agranlund/raven/hw/simm/programmer/README.md

# Raven ROM programmer

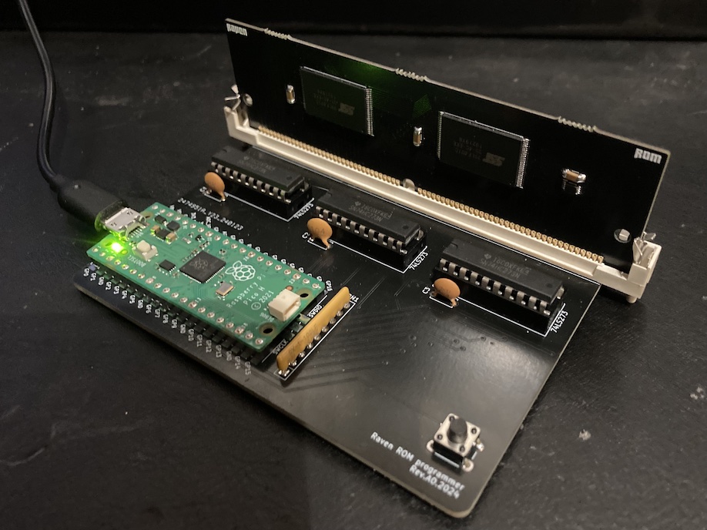
[picture p5: hw/simm/programmer/images/programmer.jpg]


## BOM

| Manufacturer | Part number | Value | Count | Ref |
|---|---|---|---|---|
| Vishay | K104K10X7RF53H5 | 0.1u | 3 | C101, C102, C103 |
| Texas Instruments | SN74HC273N | 74HC273 | 3 | U101, U103, U104 |
| Bourns | 4609X-101-102LF | 8x1K | 1 | RN101 |
| Alps Alpine | SKHHARA010 | button | 1 | SW101 |
| TE Connectivity | 5822030-3 | simm | 1 | J101 |
| Raspberry Pi | SC0915 | Pi Pico | 1 | U102 |
