agranlund/raven/hw/simm/rom_PLCC/README.md

# ROM module, socketed PLCC revision A0

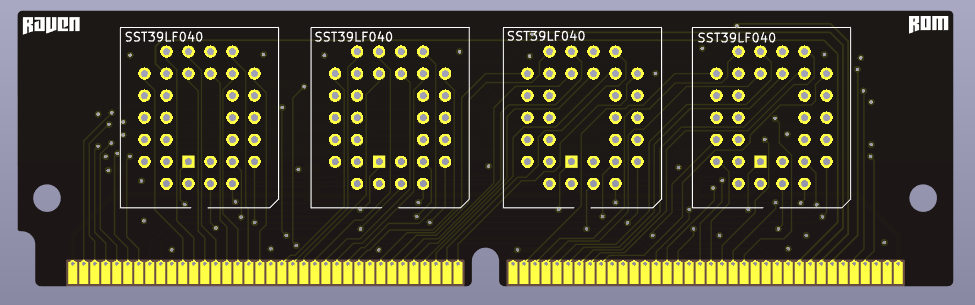
[picture p6: hw/simm/rom_PLCC/images/render.png]


Chip suggestions:
* SST39LF040-55 for 2MB
* SST39LF020-55 for 1MB

## BOM

| Manufacturer | Part number | Value | Count | Ref |
|---|---|---|---|---|
| Microchip | SST39LF040-55-4C-NHE-T | 4Mbit | 4 | U1, U2, U3, U4 |
| 3M | 8432-11B1-RK-TP | PLCC socket | 4 | U1, U2, U3, U4 |
| Kemet | C1206C104K5RACTU | 0.1u | 4 | C1, C2, C3, C4 |
