agranlund/raven/sw/dsp/asm56k/tools/readme.txt

Here are some DSP-Cross Development Utils - tested under 32bit and 64bit Linux

cldlod: 
  based upon original Motorola sources; 64bit fixed by me
  usage: cldlod cldfile [lodfile]

lod2p56:
  based upon the original Atari sources
  usage: lod2p56 lodfile [p56file]
