agranlund/raven/hw/raven/a1/upgrades/ideswap/README.md

# IDE Byteswap adapter

Converts an IDE interface between Intel and Motorola format (swaps high and low bytes)

Can be useful if you want Raven to have a legacy Atari (Motorola) IDE interface rather than the standard Intel interface it comes with.

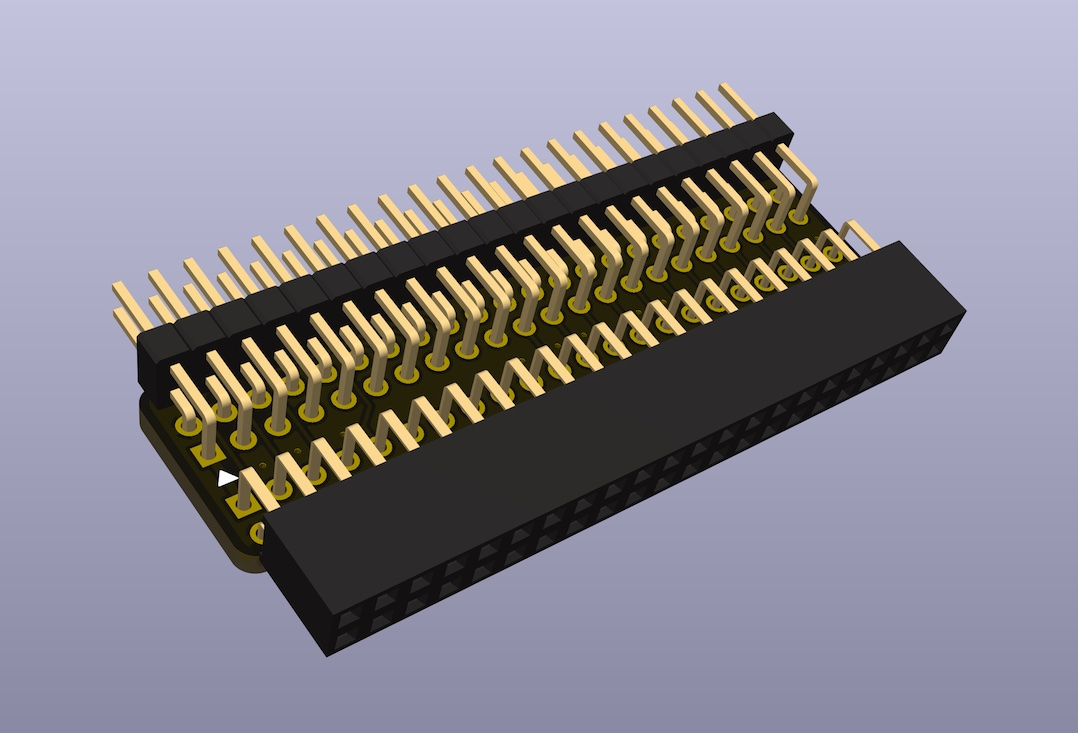
[picture p7: hw/raven/a1/upgrades/ideswap/ideswap.png]


## BOM

| Manufacturer  | Part number | Qty | Ref | Note |
|---|---|-----|---|---|
| Samtec | SQT-122-01-F-D-RA | 1 | J102 | Female right-angle |
| Amphenol | 58102-G61-22LF | 1 | J101 | Male right-angle |

(*) Molex 87833-4420 can be used if a shrouded male right-angle header is preferred.
