agranlund/raven/hw/raven/a1/upgrades/ckbd/README.md

# Eiffel upgrade module (rev.d) for Raven.A1

- Plugs into the Eiffel socket instead of the Eiffel PIC.
- Retains support for PS/2 mouse+keyboard, joystick and motherboard temperature sensor.
- Adds USB mouse and keyboard support on an internal USB header.
- Adds support for legacy Atari and Amiga mice (*)
- Adds support for reading CPU temperature (*)
- Adds support for software controlled shutdown (*)

### Firmware:
Binary, sourcecode, and programming instructions can be found here:
* [ckbd firmware](../../../../fw/ckbd/) 

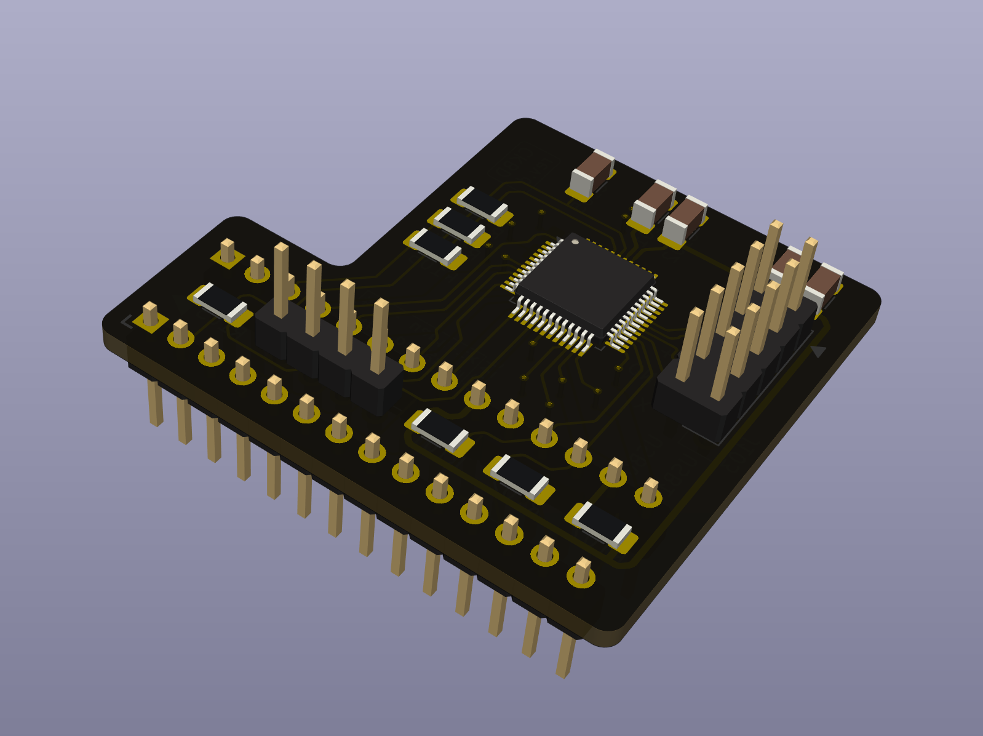
[picture p8: hw/raven/a1/upgrades/ckbd/ckbd.png]


(*) Features marked with an asterix requires soldering patch wires on the motherboard.
All solder points are available on through hole components and can be done on the underside of the motherboard.

#### Support for right mouse button on Legacy mice (not needed for USB or PS2)
- J606:A9  <-> J606:B6 (mouse right button - joystick1 fire button)
#### Support for CPU temperature readout
- U107:M15 <-> U107:M16 (CPU Therm1 - GND)
- U107:L15 <-> U301:26 (CPU Therm0 - Eiffel:Temp2)
#### Support for software controlled shutdown
- SW201:2 <-> U301:25 (PWR switch - Eiffel:PwrOff)

## BOM

| Manufacturer  | Part number | Value | Qty | Ref | Note |
|---|---|---|-----|---|---|
| WCH | CH559L | CH559L | 1 | U101 | |
| Yageo | RT1206FRE0710KL | 10K | 3 | R103,R105,R106 | |
| Yageo | RT1206FRE071KL | 1K | 4 | R101,R102,R104,R107 | |
| Kemet | C1206C105K4RACTU  | 1u | 2 | C103,C104 | |
| Kemet | C1206C104K5RACTU  | 0.1u | 2 | C102,C105 | |
| Kemet | C1206C334K5RACTU  | 0.33u | 1 | C101 | |
| ? | pinheader round | 1x14 | 2 | J101,J102 | (1)  |
| ? | pinheader square  | 2x5 | 1 | J103 | (2)  |
| ? | pinheader square  | 1x4 | 1 | J104 | (2)  |

(1) J101,J102 needs to be round machined pins that can fit in a dip socket.
40-pin breakaway strips can be found here:
https://www.exxosforum.co.uk/atari/store2/#0132

(2) J103,J104 are standard square pin headers which can be found anywhere.
40-pin breakaway strips can be found here:
https://www.exxosforum.co.uk/atari/store2/#0158

## Notes for previous rev.c boards:

The eiffel controlled fan does not work in the previous version of this board.

This can be fixed by soldering a ~1K resistor connecting pins FAN1 and +5V which are both found on the right row of the Eiffel connector.
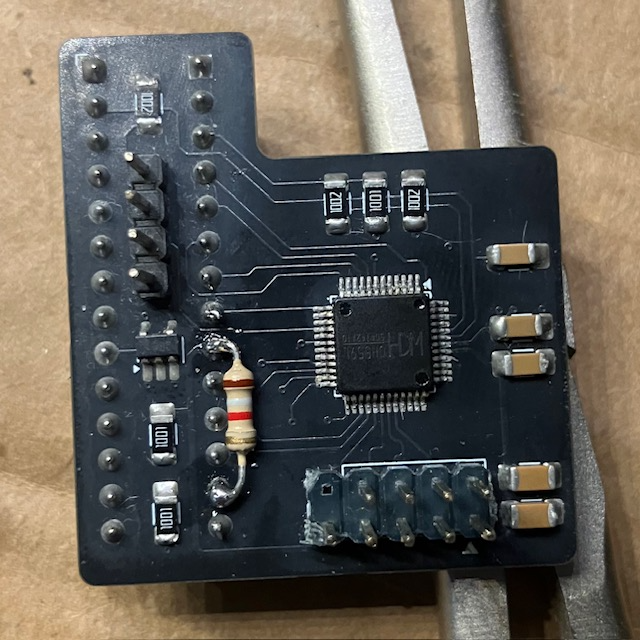
[picture p9: hw/raven/a1/upgrades/ckbd/ckbd_revc_fix.png]
