agranlund/raven/hw/isa/template_16bit/README.md

# Blank template
(untested)

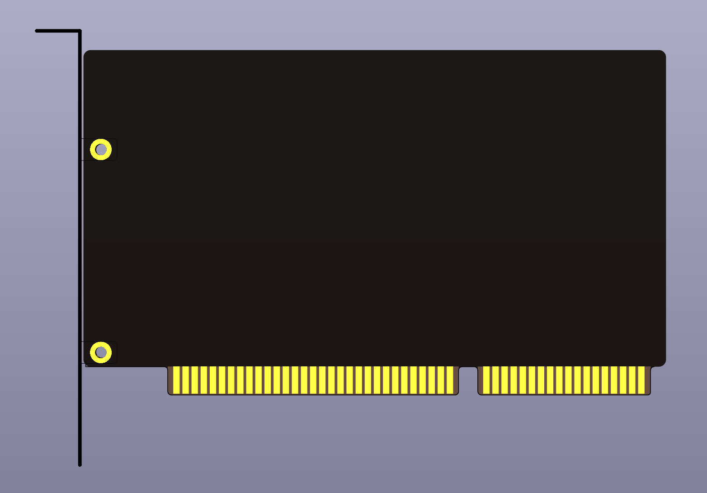
[picture p15: hw/isa/template_16bit/images/render.png]
