agranlund/raven/sw/tools/mon/readme.txt

Raven monitor shell

usage: mon <parameter>

Interact with Raven debug monitor from the TOS shell.
Same functionality as when pressing the NMI switch and doing so over a serial connection.
Parameters can be passed to execute a single command instead of interacting with the full shell.

This file is free software  you can redistribute it and/or modify
it under the terms of the GNU General Public License as published by
the Free Software Foundation  either version 2, or (at your option)
any later version.

This file is distributed in the hope that it will be useful,
but WITHOUT ANY WARRANTY  without even the implied warranty of
MERCHANTABILITY or FITNESS FOR A PARTICULAR PURPOSE.  See the
GNU General Public License for more details.

You should have received a copy of the GNU General Public License
along with this program  if not, write to the Free Software
Foundation, Inc., 675 Mass Ave, Cambridge, MA 02139, USA.
