agranlund/raven/hw/simm/ram_8M10/README.md

# RAM module: 8MB / 10ns

# !DO NOT USE! NOT YET SUPPORTED BY RAVEN FIRMWARE

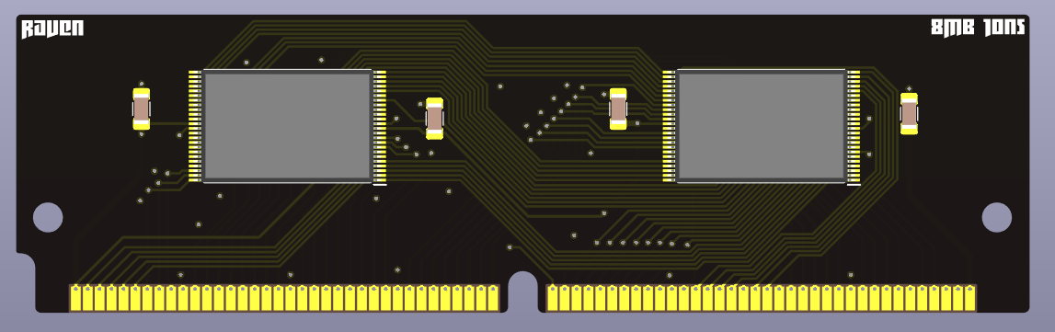
[picture p19: hw/simm/ram_8M10/images/render.png]


## BOM

| Manufacturer | Part number | Value | Count | Ref |
|---|---|---|---|---|
| ISSI | IS61WV204816BLL-10TLI | 16x2MBit | 2 | IC1, IC2 |
| Kemet | C1206C104K5RACTU | 0.1u | 4 | C1, C2, C3, C4 |
