agranlund/raven/hw/simm/breakout/README.md

# Debug module (untested)

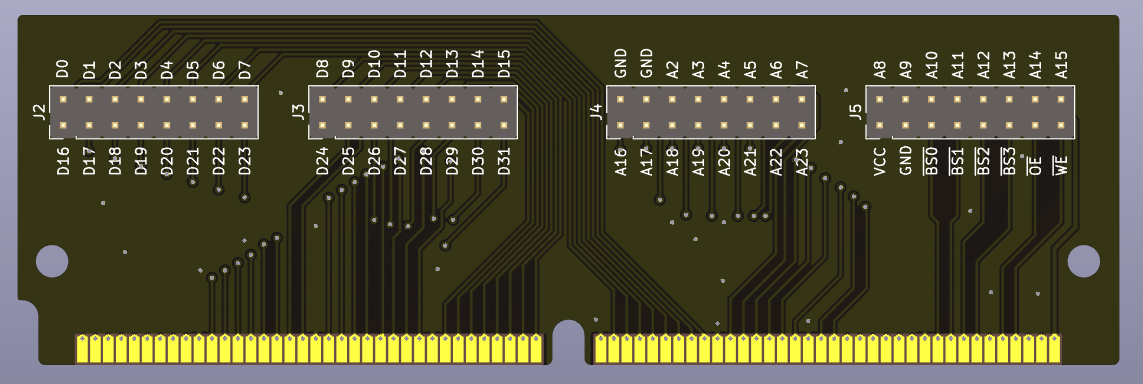
[picture p20: hw/simm/breakout/images/render.png]
