agranlund/raven/hw/simm/ram_16M55/README.md

# RAM module: 16MB / 55ns

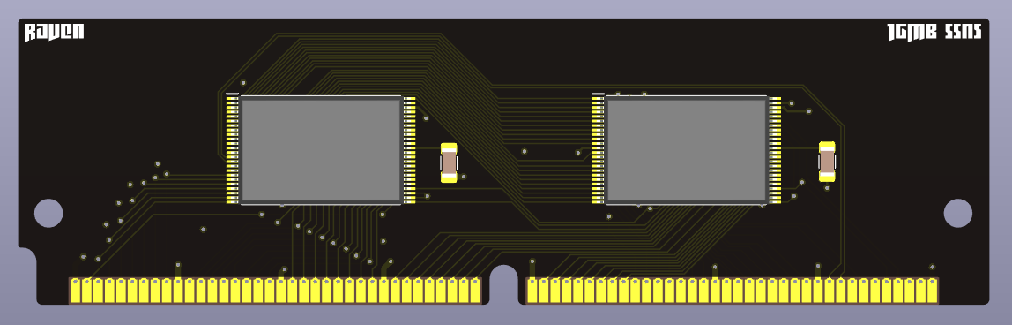
[picture p21: hw/simm/ram_16M55/images/render.png]


## BOM

| Manufacturer | Part number | Value | Count | Ref |
|---|---|---|---|---|
| Alliance Memory | AS6C6416-55TIN | 16x4MBit | 2 | IC1, IC2 |
| Kemet | C1206C104K5RACTU | 0.1u | 2 | C1, C2 |
