agranlund/raven/doc/img/board.gif

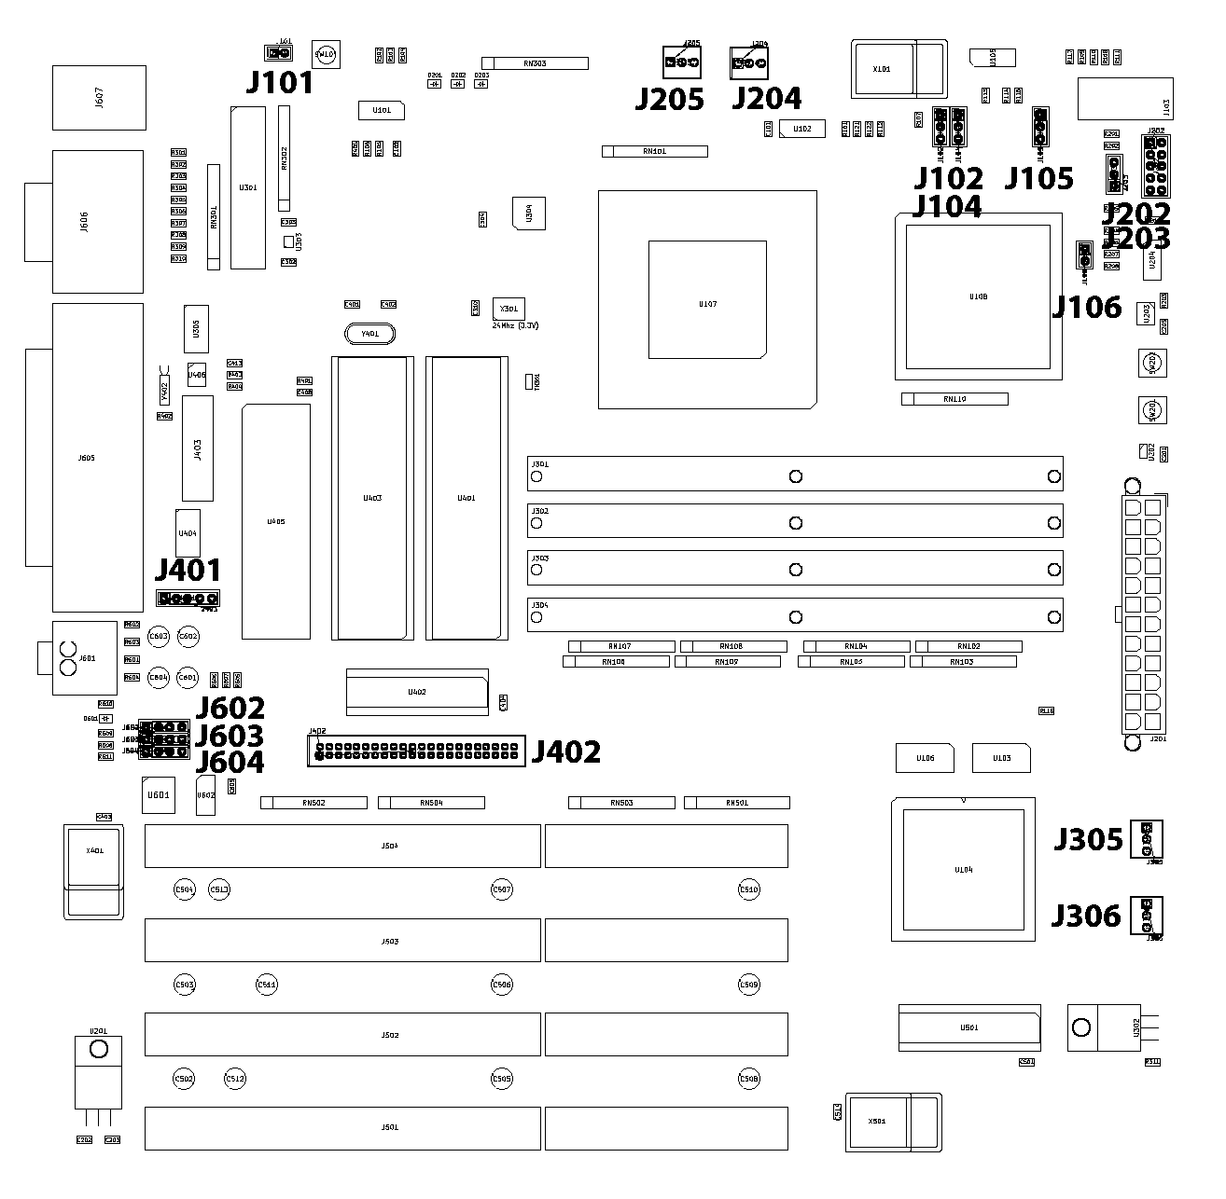
doc/img/board.gif
