agranlund/raven/doc/img/com.gif

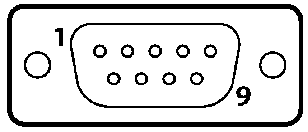
doc/img/com.gif
