agranlund/raven/doc/img/ide.gif

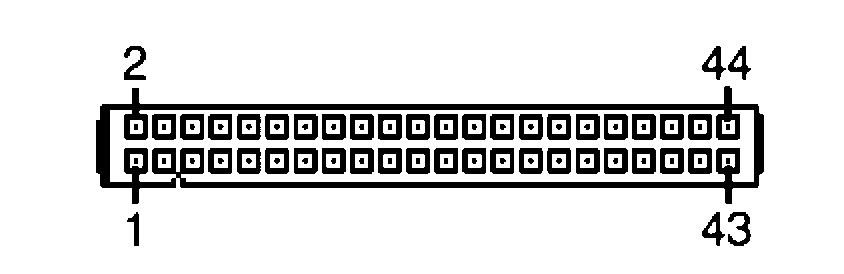
doc/img/ide.gif
