agranlund/raven/doc/img/ps2.gif

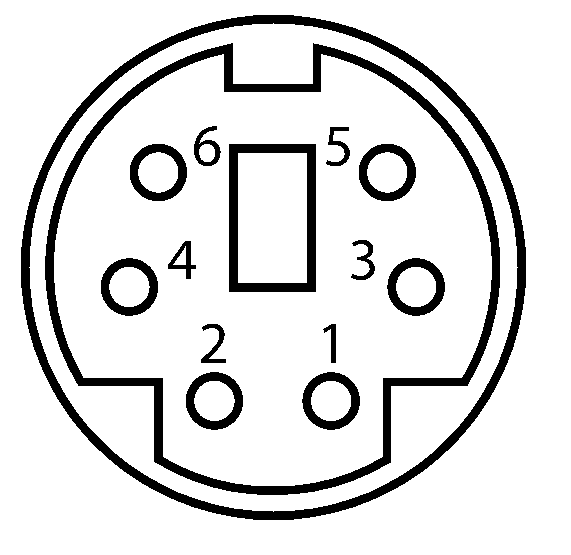
doc/img/ps2.gif
