agranlund/raven/doc/img/simm.gif

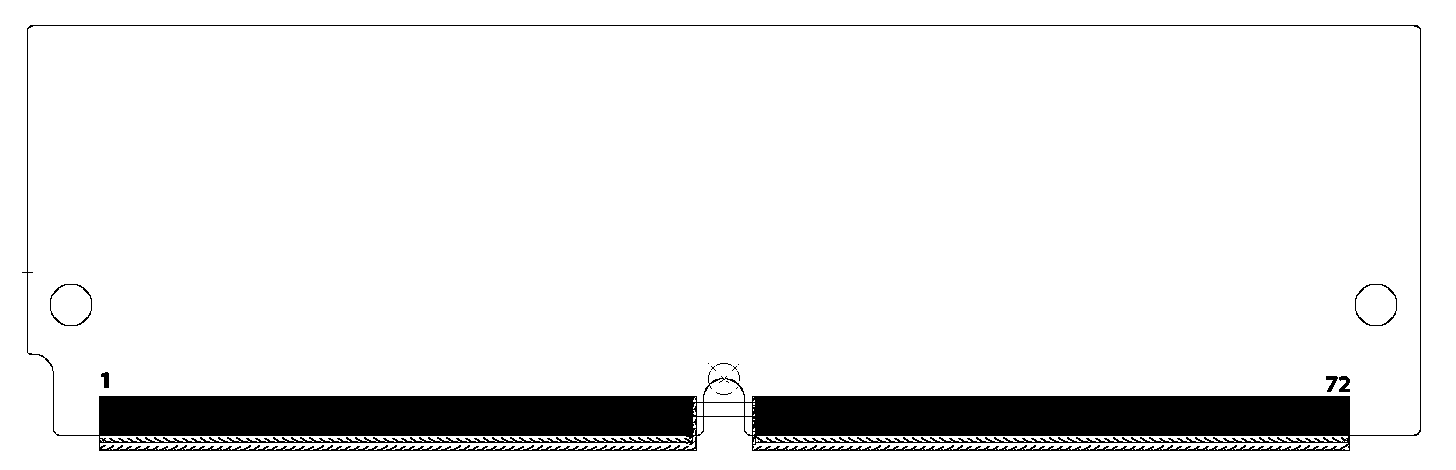
doc/img/simm.gif
