agranlund/raven/hw/raven/a0/images/raven_a0.jpg

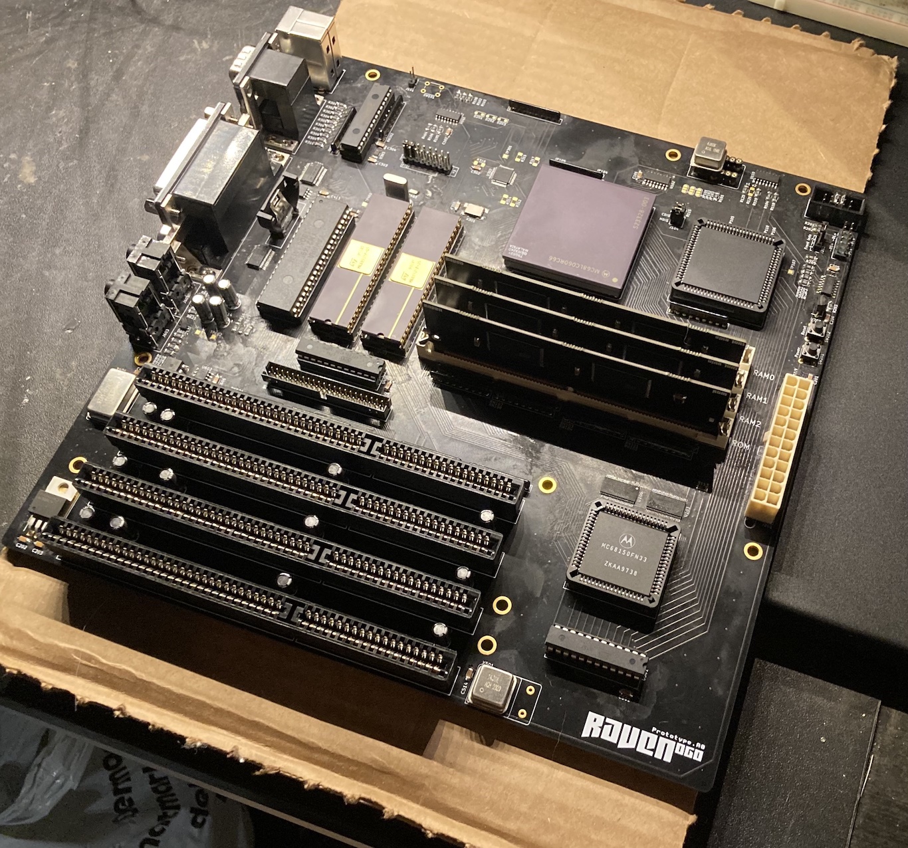
hw/raven/a0/images/raven_a0.jpg
