agranlund/raven/hw/raven/a0/images/raven_a0_cased1.jpg

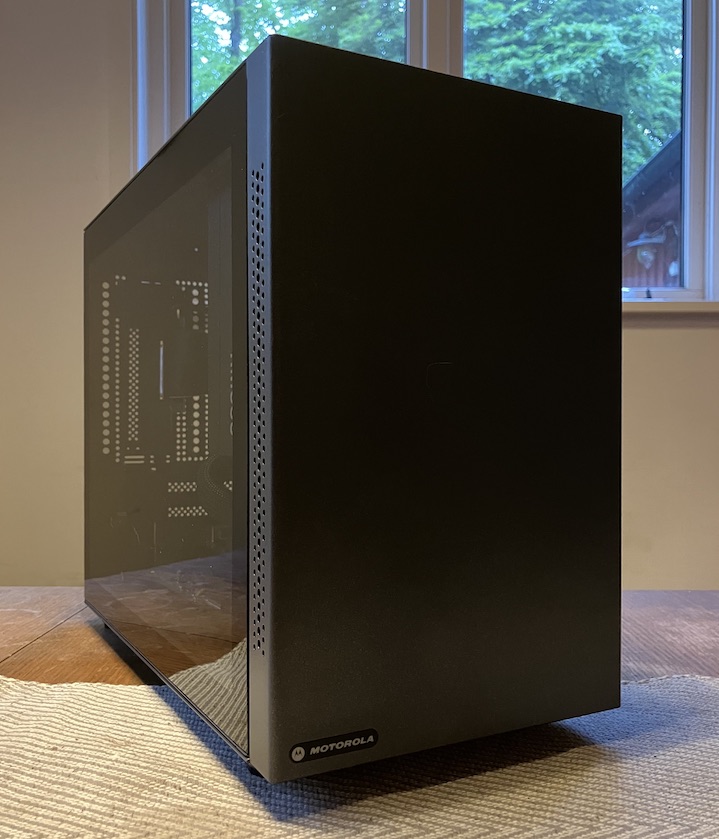
hw/raven/a0/images/raven_a0_cased1.jpg
