agranlund/raven/hw/simm/template/images/render.png

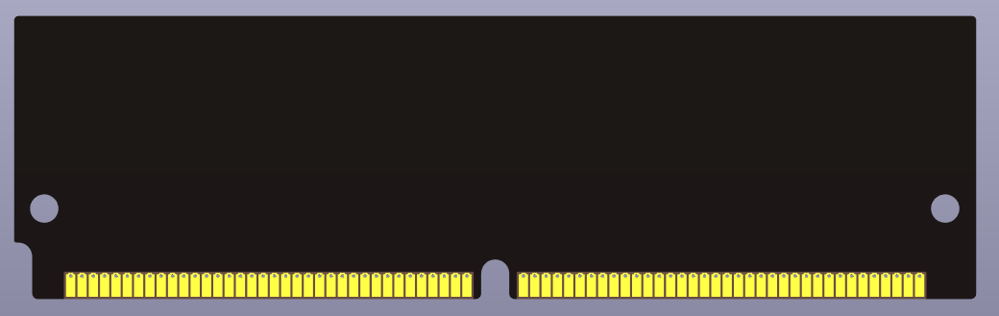
hw/simm/template/images/render.png
