agranlund/raven/sw/isa/drivers/picogus/hw-common/parts/USB-microB_U254-051T-4BH83-F1S.step

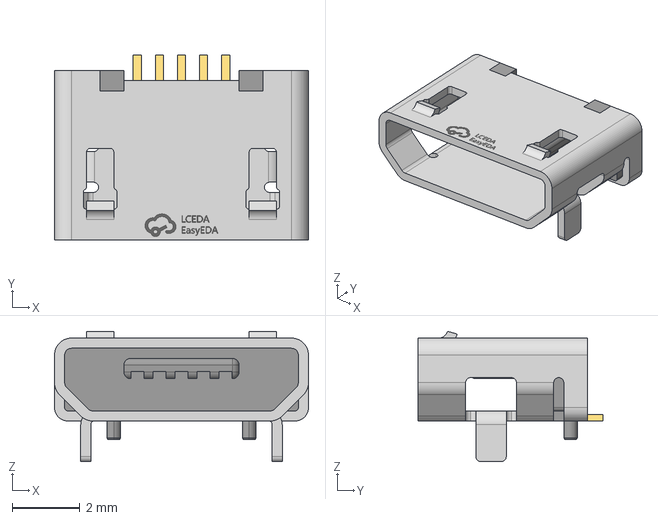
[picture p57: CAD file, 2024-07-06]
sw/isa/drivers/picogus/hw-common/parts/USB-microB_U254-051T-4BH83-F1S.step
7.50 x 5.45 x 3.85 mm
