agranlund/raven/sw/isa/drivers/picogus/isa-hand386 adapter/parts/RK10J12R0A0B.stp

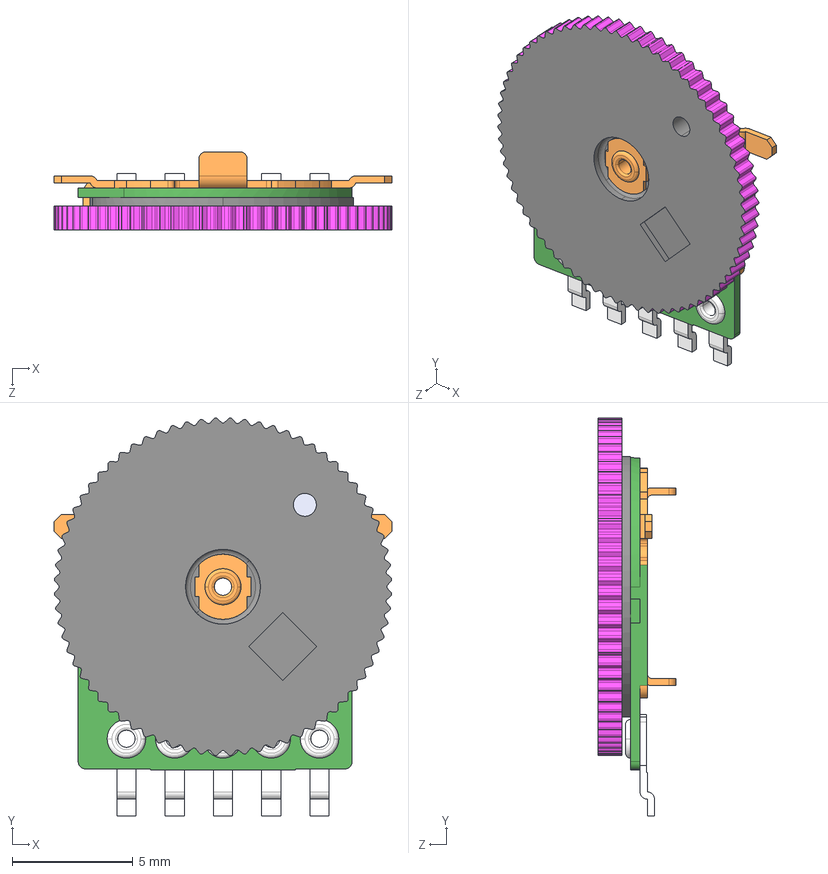
[picture p58: CAD file, 2024-07-06]
sw/isa/drivers/picogus/isa-hand386 adapter/parts/RK10J12R0A0B.stp
14.0 x 16.5 x 3.25 mm
