agranlund/raven/sw/isa/drivers/picogus/hw-common/parts/RK10J12R0A0B.step

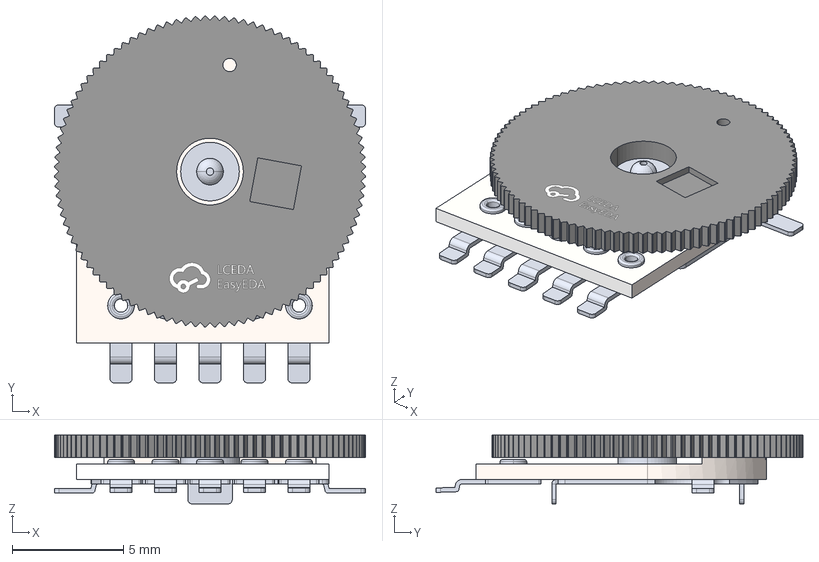
[picture p59: CAD file, 2024-07-06]
sw/isa/drivers/picogus/hw-common/parts/RK10J12R0A0B.step
14.0 x 16.5 x 3.10 mm
