agranlund/raven/sw/isa/drivers/picogus/hw-common/parts/keystone-9202-maxconnector.step

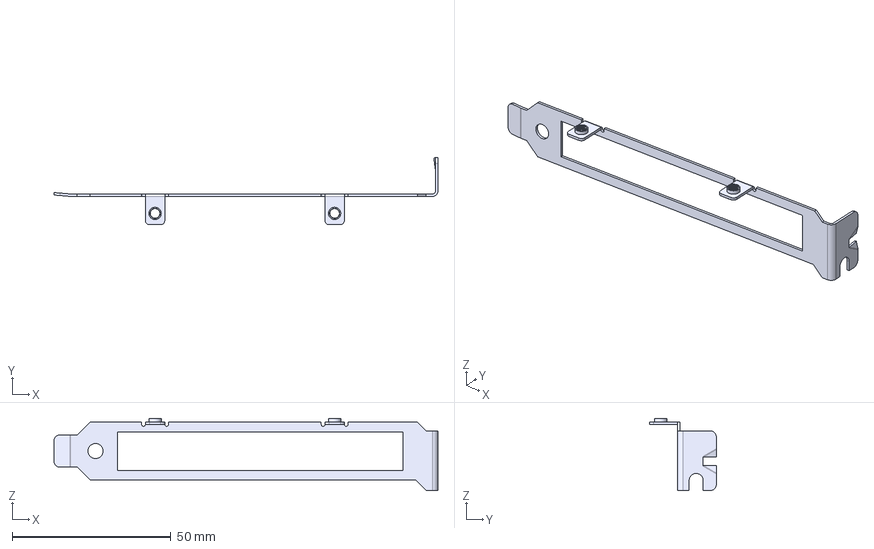
[picture p60: CAD file, 2024-07-06]
sw/isa/drivers/picogus/hw-common/parts/keystone-9202-maxconnector.step
120.9 x 21.2 x 22.7 mm
