agranlund/raven/sw/isa/drivers/picogus/hw-common/parts/PJ-210B.step

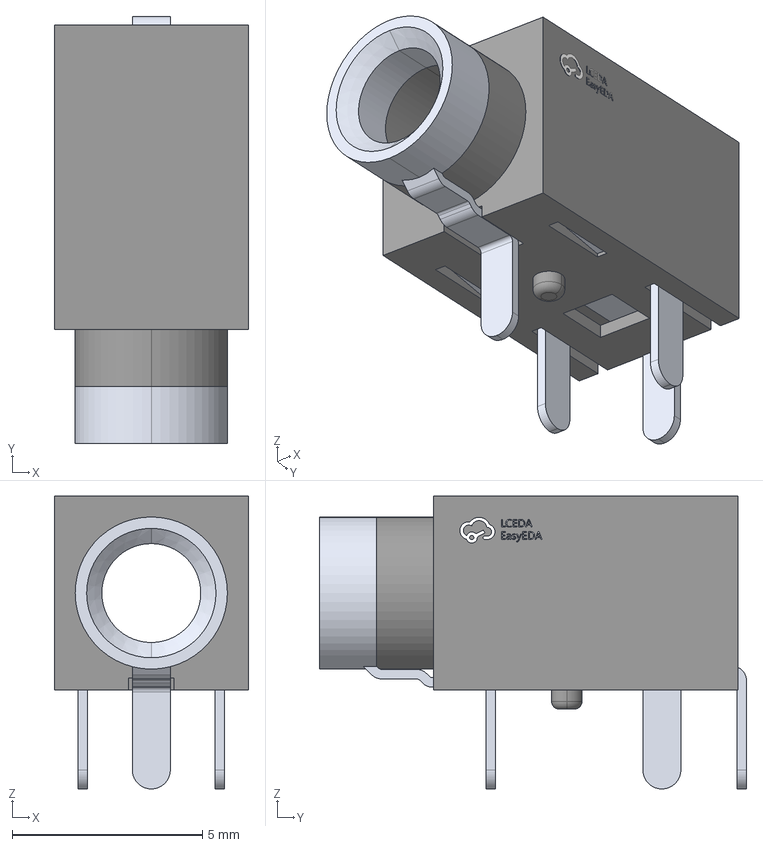
[picture p61: CAD file, 2024-07-06]
sw/isa/drivers/picogus/hw-common/parts/PJ-210B.step
5.11 x 11.2 x 7.70 mm
