agranlund/raven/sw/isa/drivers/picogus/hw-common/parts/TL3305BFxxxxG.stp

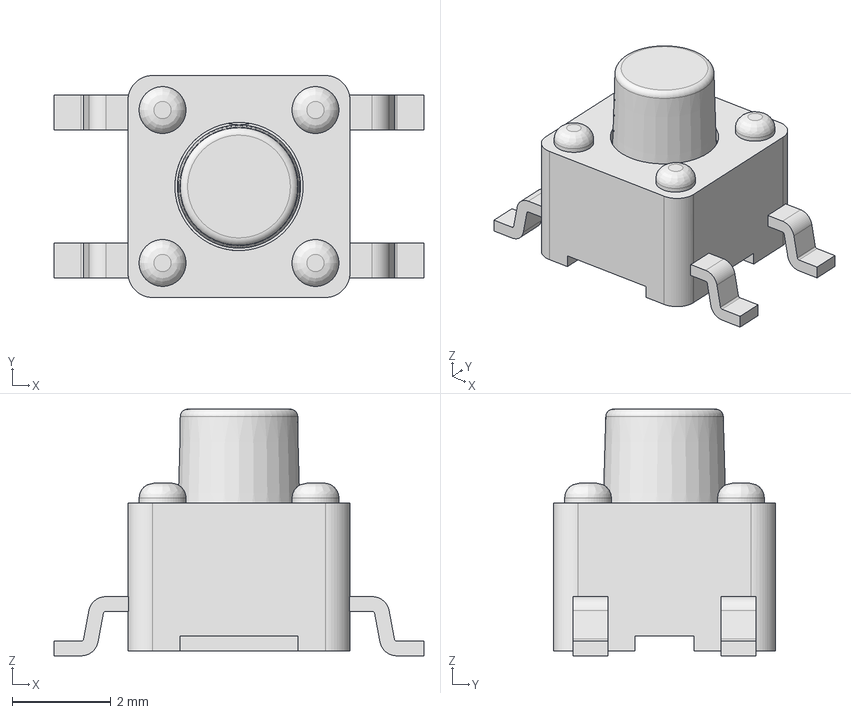
[picture p62: CAD file, 2024-07-06]
sw/isa/drivers/picogus/hw-common/parts/TL3305BFxxxxG.stp
7.50 x 4.50 x 5.00 mm
