agranlund/raven/sw/isa/drivers/picogus/hw-common/parts/CUI_DEVICES_SJ1-3533NG.step

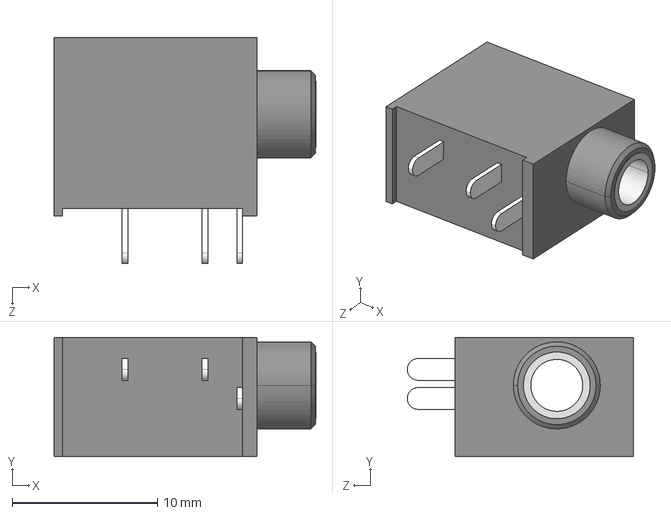
[picture p63: CAD file, 2024-07-06]
sw/isa/drivers/picogus/hw-common/parts/CUI_DEVICES_SJ1-3533NG.step
18.1 x 8.20 x 15.6 mm
