agranlund/raven/sw/isa/drivers/picogus/hw-common/parts/USB-A_902-131A1011D10100.step

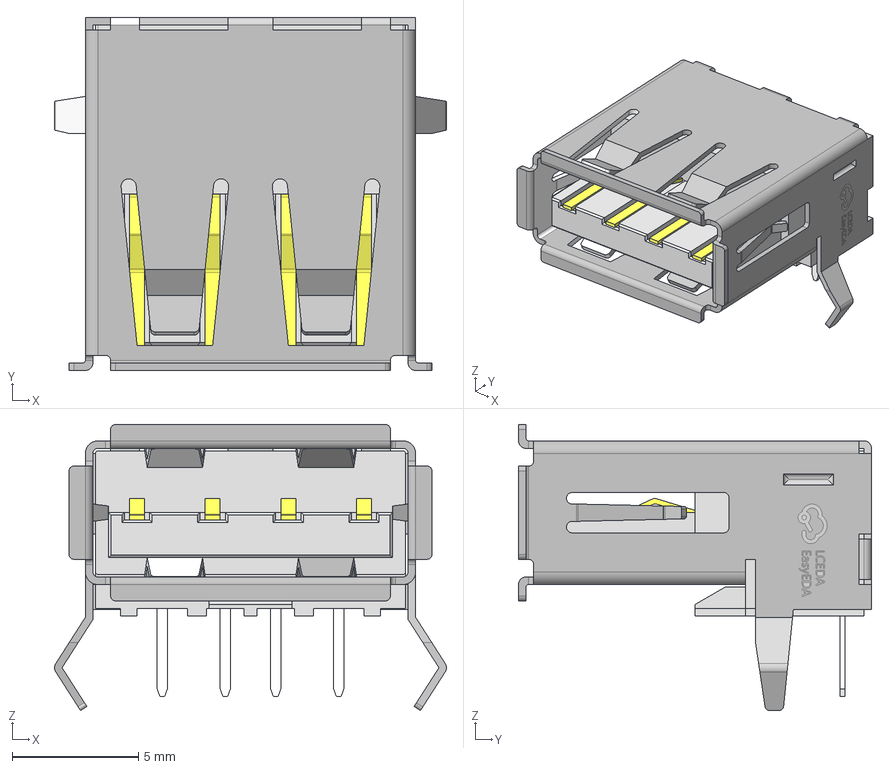
[picture p64: CAD file, 2024-07-06]
sw/isa/drivers/picogus/hw-common/parts/USB-A_902-131A1011D10100.step
15.5 x 14.0 x 11.3 mm
