agranlund/raven/sw/rvnova/test/scroll.bmp

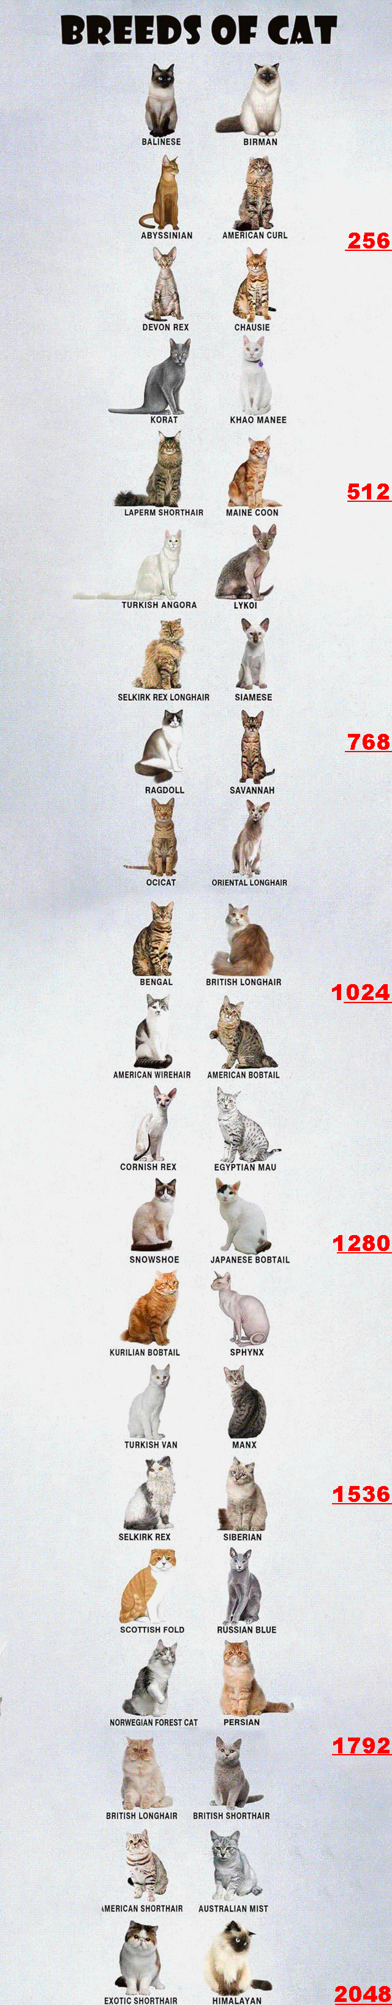
sw/rvnova/test/scroll.bmp
