agranlund/raven/hw/simm/breakout/simm72_breakout.kicad_pcb

## KiCad design hw/simm/breakout/simm72_breakout.kicad_pcb (2024-06-06)

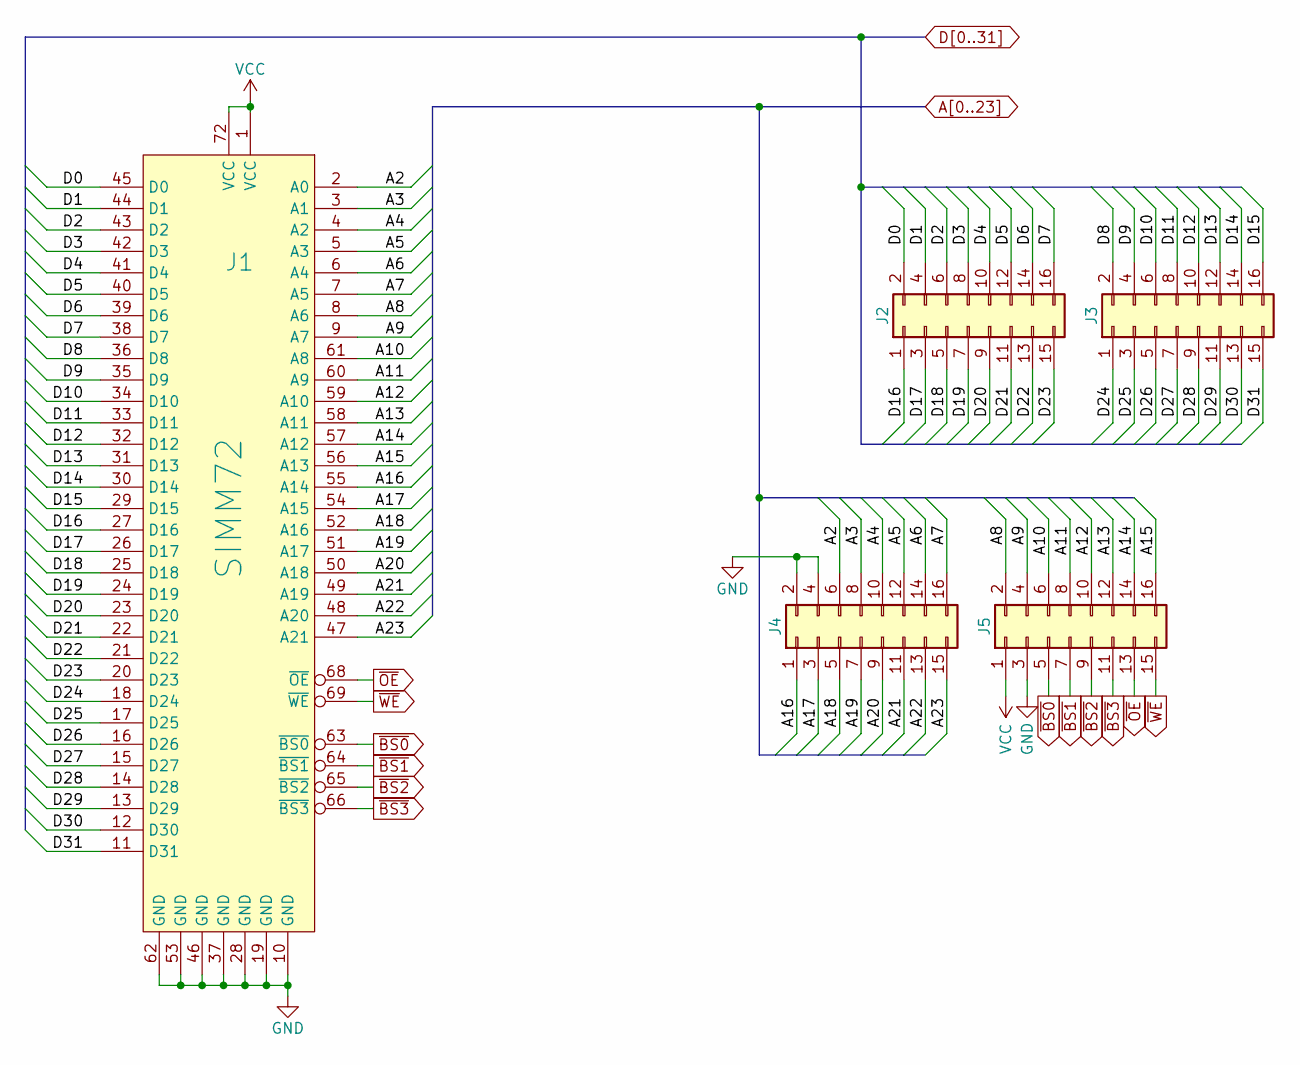
[picture p116: schematic simm72_breakout.kicad_sch, Raven SIMM breakout]

Parts:
J1: SIMM72; SIMM72_edge
J2, J3, J4, J5: Conn_02x08_Row_Letter_Last; PinHeader_2x08_P2.54mm_Vertical

Connections:
A2: J1.2 (A0), J4.6
A3: J1.3 (A1), J4.8
A4: J1.4 (A2), J4.10
A5: J1.5 (A3), J4.12
A6: J1.6 (A4), J4.14
A7: J1.7 (A5), J4.16
A8: J1.8 (A6), J5.2
A9: J1.9 (A7), J5.4
A10: J1.61 (A8), J5.6
A11: J1.60 (A9), J5.8
A12: J1.59 (A10), J5.10
A13: J1.58 (A11), J5.12
A14: J1.57 (A12), J5.14
A15: J1.56 (A13), J5.16
A16: J1.55 (A14), J4.1
A17: J1.54 (A15), J4.3
A18: J1.52 (A16), J4.5
A19: J1.51 (A17), J4.7
A20: J1.50 (A18), J4.9
A21: J1.49 (A19), J4.11
A22: J1.48 (A20), J4.13
A23: J1.47 (A21), J4.15
D0: J1.45 (D0), J2.2
D1: J1.44 (D1), J2.4
D2: J1.43 (D2), J2.6
D3: J1.42 (D3), J2.8
D4: J1.41 (D4), J2.10
D5: J1.40 (D5), J2.12
D6: J1.39 (D6), J2.14
D7: J1.38 (D7), J2.16
D8: J1.36 (D8), J3.2
D9: J1.35 (D9), J3.4
D10: J1.34 (D10), J3.6
D11: J1.33 (D11), J3.8
D12: J1.32 (D12), J3.10
D13: J1.31 (D13), J3.12
D14: J1.30 (D14), J3.14
D15: J1.29 (D15), J3.16
D16: J1.27 (D16), J2.1
D17: J1.26 (D17), J2.3
D18: J1.25 (D18), J2.5
D19: J1.24 (D19), J2.7
D20: J1.23 (D20), J2.9
D21: J1.22 (D21), J2.11
D22: J1.21 (D22), J2.13
D23: J1.20 (D23), J2.15
D24: J1.18 (D24), J3.1
D25: J1.17 (D25), J3.3
D26: J1.16 (D26), J3.5
D27: J1.15 (D27), J3.7
D28: J1.14 (D28), J3.9
D29: J1.13 (D29), J3.11
D30: J1.12 (D30), J3.13
D31: J1.11 (D31), J3.15
GND: J1.10 (GND), J1.19 (GND), J1.28 (GND), J1.37 (GND), J1.46 (GND), J1.53 (GND), J1.62 (GND), J4.2, J4.4, J5.3
VCC: J1.1 (VCC), J1.72 (VCC), J5.1
~BS0: J1.63 (~BS0), J5.5
~BS1: J1.64 (~BS1), J5.7
~BS2: J1.65 (~BS2), J5.9
~BS3: J1.66 (~BS3), J5.11
~OE: J1.68 (~OE), J5.13
~WE: J1.69 (~WE), J5.15

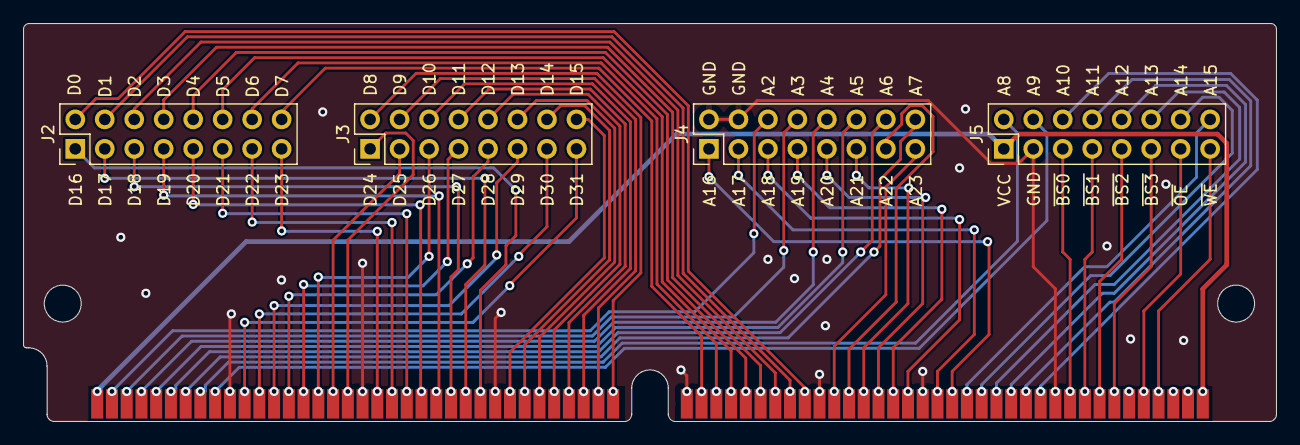
[picture p117: board simm72_breakout.kicad_pcb from above]

Board: 2 copper layers, 108.0 x 34.3 mm, 5 parts (0 on the bottom side), 62 nets.
