agranlund/raven/sw/purec/src/crosstos/abin/pc/INCLUDE/TOS.H

#define __TOS
typedef struct
{
        unsigned char maxlen;
        unsigned char actuallen;
        char    buffer[255];
} LINE;
typedef struct
{
    char            d_reserved[21];
    unsigned char   d_attrib;
    unsigned int    d_time;
    unsigned int    d_date;
    unsigned long   d_length;
    char            d_fname[14];
} DTA;
typedef struct
{
    unsigned long   b_free;
    unsigned long   b_total;
    unsigned long   b_secsiz;
    unsigned long   b_clsiz;
} DISKINFO;
typedef struct baspag
{
        void    *p_lowtpa;
        void    *p_hitpa;
        void    *p_tbase;
        long    p_tlen;
        void    *p_dbase;
        long    p_dlen;
        void    *p_bbase;
        long    p_blen;
        DTA     *p_dta;
        struct baspag *p_parent;
        long    p_resrvd0;
        char    *p_env;
        char    p_stdfh[6];
        char    p_resrvd1;
        char    p_curdrv;
        long    p_resrvd2[18];
        char    p_cmdlin[128];
} BASPAG;
typedef struct
{
        int     recsiz;
        int     clsiz;
        int     clsizb;
        int     rdlen;
        int     fsiz;
        int     fatrec;
        int     datrec;
        int     numcl;
        int     bflags;
} BPB;
typedef struct
{
        unsigned int  time;
        unsigned int  date;
} DOSTIME;
typedef struct
{
        void    *ibuf;
        int     ibufsiz;
        int     ibufhd;
        int     ibuftl;
        int     ibuflow;
        int     ibufhi;
} IOREC;
typedef struct
{
        void    (*kb_midivec)();
        void    (*kb_vkbderr)();
        void    (*kb_vmiderr)();
        void    (*kb_statvec)();
        void    (*kb_mousevec)();
        void    (*kb_clockvec)();
        void    (*kb_joyvec)();
        void    (*kb_midisys)();
        void    (*kb_kbdsys)();
} KBDVBASE;
typedef struct
{
        unsigned char   length;
        char            command_tail[128];
} COMMAND;
typedef struct
{
        char    topmode;
        char    buttons;
        char    x_scale;
        char    y_scale;
        int     x_max;
        int     y_max;
        int     x_start;
        int     y_start;
} MOUSE;
typedef struct
{
        void    *pb_scrptr;
        int     pb_offset;
        int     pb_width;
        int     pb_height;
        int     pb_left;
        int     pb_right;
        int     pb_screz;
        int     pb_prrez;
        void    *pb_colptr;
        int     pb_prtype;
        int     pb_prport;
        void    *pb_mask;
} PBDEF;
typedef struct
{
        char *unshift;
        char *shift;
        char *capslock;
} KEYTAB;
typedef struct __md
{
        struct __md *m_link;
        void        *m_start;
        long        m_length;
        BASPAG      *m_own;
} MD;
typedef struct
{
        MD *mp_mfl;
        MD *mp_mal;
        MD *mp_rover;
} MPB;
typedef struct
{
        int   (*Bconstat) ();
        long  (*Bconin) ();
        int   (*Bcostat) ();
        void  (*Bconout) ();
        long  (*Rsconf) ();
        IOREC *iorec;
} MAPTAB;
typedef struct
{
        MAPTAB *maptab;
        int    maptabsize;
} BCONMAP;
typedef struct _syshdr
{
    unsigned       os_entry;
    unsigned       os_version;
    void           *os_start;
    struct _syshdr *os_base;
    void           *os_membot;
    void           *os_rsv1;
    long           *os_magic;
    long           os_gendat;
    int            os_palmode;
    int            os_gendatg;
    void           *_root;
    long           *kbshift;
    BASPAG         **_run;
    void           *p_rsv2;
} SYSHDR;
#define FA_READONLY     0x01
#define FA_HIDDEN       0x02
#define FA_SYSTEM       0x04
#define FA_VOLUME       0x08
#define FA_SUBDIR       0x10
#define FA_ARCHIVE      0x20
#define FO_READ         0
#define FO_WRITE        1
#define FO_RW           2
extern BASPAG *_BasPag;
extern long _PgmSize;
long    gemdos( void, ... );
long    bios( void, ... );
long    xbios( void, ... );
void    Pterm0( void );
long    Cconin( void );
void    Cconout( int c );
int     Cauxin( void );
void    Cauxout( int c );
int     Cprnout( int c );
long    Crawio( int w );
long    Crawcin( void );
long    Cnecin( void );
int     Cconws( const char *buf );
void    Cconrs( LINE *buf );
int     Cconis( void );
long    Dsetdrv( int drv );
int     Cconos( void );
int     Cprnos( void );
int     Cauxis( void );
int     Cauxos( void );
int     Dgetdrv( void );
void    Fsetdta( DTA *buf );
long    Super( void *stack );
unsigned int  Tgetdate( void );
unsigned int Tsetdate( unsigned int date );
unsigned int  Tgettime( void );
unsigned int  Tsettime( unsigned int time );
DTA     *Fgetdta( void );
int     Sversion( void );
void    Ptermres( long keepcnt, int retcode );
int     Dfree( DISKINFO *buf, int driveno );
int     Dcreate( const char *path );
int     Ddelete( const char *path );
int     Dsetpath( const char *path );
long    Fcreate( const char *filename, int attr );
long    Fopen( const char *filename, int mode );
int     Fclose( int handle );
long    Fread( int handle, long count, void *buf );
long    Fwrite( int handle, long count, void *buf );
int     Fdelete( const char *filename );
long    Fseek( long offset, int handle, int seekmode );
int     Fattrib( const char *filename, int wflag, int attrib );
long    Fdup( int handle );
long    Fforce( int stch, int nonstdh );
int     Dgetpath( char *path, int driveno );
void    *Malloc( long number );
int     Mfree( void *block );
int     Mshrink( int zero, void *block, long newsiz );
long    Pexec( int mode, char *ptr1, void *ptr2, void *ptr3 );
void    Pterm( int retcode );
int     Fsfirst( const char *filename, int attr );
int     Fsnext( void );
int     Frename( int zero, const char *oldname, const char *newname );
int     Fdatime( DOSTIME *timeptr, int handle, int wflag );
void    *Mxalloc( long number, int mode );
long    Maddalt( void *start, long size );
long    Flock( int handle, int mode, long start, long length );
void    Getmpb( MPB *ptr );
int     Bconstat( int dev );
long    Bconin( int dev );
void    Bconout( int dev, int c );
long    Rwabs( int rwflag, void *buf, int cnt, int recnr, int dev );
void    (*Setexc( int number, void (*exchdlr)() )) ();
long    Tickcal( void );
BPB     *Getbpb( int dev );
long    Bcostat( int dev );
long    Mediach( int dev );
long    Drvmap( void );
long    Kbshift( int mode );
void    Initmouse( int type, MOUSE *par, void (*mousevec)() );
void    *Ssbrk( int count );
void    *Physbase( void );
void    *Logbase( void );
int     Getrez( void );
void    Setscreen( void *laddr, void *paddr, int rez );
void    Setpalette( void *pallptr );
int     Setcolor( int colornum, int color );
int     Floprd( void *buf, void *filler, int devno, int sectno,
               int trackno, int sideno, int count );
int     Flopwr( void *buf, void *filler, int devno, int sectno,
               int trackno, int sideno, int count );
int     Flopfmt( void *buf, void *filler, int devno, int spt, int trackno,
                int sideno, int interlv, long magic, int virgin );
void    Midiws( int cnt, void *ptr );
void    Mfpint( int erno, void (*vector)() );
IOREC   *Iorec( int dev );
long    Rsconf( int baud, int ctr, int ucr, int rsr, int tsr, int scr );
KEYTAB  *Keytbl( void *unshift, void *shift, void *capslock );
long    Random( void );
void    Protobt( void *buf, long serialno, int disktype, int execflag );
int     Flopver( void *buf, void *filler, int devno, int sectno,
                int trackno, int sideno, int count );
void    Scrdmp( void );
int     Cursconf( int func, int rate );
void    Settime( unsigned long time );
unsigned long  Gettime( void );
void    Bioskeys( void );
void    Ikbdws( int count, void *ptr );
void    Jdisint( int number );
void    Jenabint( int number );
char    Giaccess( char data, int regno );
void    Offgibit( int bitno );
void    Ongibit( int bitno );
void    Xbtimer( int timer, int control, int data, void (*vector)() );
void    *Dosound( void *buf );
int     Setprt( int config );
KBDVBASE *Kbdvbase( void );
int     Kbrate( int initial, int repeat );
void    Prtblk( PBDEF *par );
void    Vsync( void );
long    Supexec( long (*func)() );
void    Puntaes( void );
int     Floprate( int devno, int newrate );
int     Blitmode( int mode );
int     DMAread( long sector, int count, void *buffer, int devno );
int     DMAwrite( long sector, int count, void *buffer, int devno );
int     NVMaccess( int opcode, int start, int count, void *buffer );
long    Bconmap( int devno );
int     Esetshift( int shftMode );
int     Egetshift( void );
int     EsetBank( int bankNum );
int     EsetColor( int colorNum, int color );
void    EsetPalette( int colorNum, int count, int *palettePtr );
void    EgetPalette( int colorNum, int count, int *palettePtr );
int     EsetGray( int swtch );
int     EsetSmear( int swtch );
#define NSIG       31
#define SIGNULL     0
#define SIGHUP      1
#define SIGINT      2
#define SIGQUIT     3
#define SIGILL      4
#define SIGTRAP     5
#define SIGABRT     6
#define SIGPRIV     7
#define SIGFPE      8
#define SIGKILL     9
#define SIGBUS     10
#define SIGSEGV    11
#define SIGSYS     12
#define SIGPIPE    13
#define SIGALRM    14
#define SIGTERM    15
#define SIGURG     16
#define SIGSTOP    17
#define SIGTSTP    18
#define SIGCONT    19
#define SIGCHLD    20
#define SIGTTIN    21
#define SIGTTOU    22
#define SIGIO      23
#define SIGXCPU    24
#define SIGXFSZ    25
#define SIGVTALRM  26
#define SIGPROF    27
#define SIGWINCH   28
#define SIGUSR1    29
#define SIGUSR2    30
#define SIG_DFL    0
#define SIG_IGN    1
#define S_IFMT  0170000
#define S_IFCHR 0020000
#define S_IFDIR 0040000
#define S_IFREG 0100000
#define S_IFIFO 0120000
#define S_IMEM  0140000
#define S_IFLNK 0160000
#define S_ISUID 04000
#define S_ISGID 02000
#define S_ISVTX 01000
#define S_IRUSR         0400
#define S_IWUSR         0200
#define S_IXUSR         0100
#define S_IRGRP         0040
#define S_IWGRP         0020
#define S_IXGRP         0010
#define S_IROTH         0004
#define S_IWOTH         0002
#define S_IXOTH         0001
#define DEFAULT_DIRMODE (0777)
#define DEFAULT_MODE    (0666)
typedef struct
{
        long     msg1;
        long     msg2;
        int      pid;
} MSG;
typedef struct
{
        unsigned int   mode;
        long           index;
        unsigned int   dev;
        unsigned int   reserved1;
        unsigned int   nlink;
        unsigned int   uid;
        unsigned int   gid;
        long           size;
        long           blksize;
        long           nblocks;
        int            mtime;
        int            mdate;
        int            atime;
        int            adate;
        int            ctime;
        int            cdate;
        int            attr;
        int            reserved2;
        long           reserved3[2];
} XATTR;
#define SA_NOCLDSTOP    1
typedef struct
{
        void    (*sa_handler)( long sig );
        long    sa_mask;
        int     sa_flags;
} SIGACTION;
int     Syield( void );
int     Fpipe( int *usrh );
int     Fcntl( int f, long arg, int cmd );
long    Finstat( int f );
long    Foutstat( int f );
long    Fgetchar( int f, int mode );
long    Fputchar( int f, long c, int mode );
long    Pwait( void );
int     Pnice( int delta );
int     Pgetpid( void );
int     Pgetppid( void );
int     Pgetpgrp( void );
int     Psetpgrp( int pid, int newgrp );
int     Pgetuid( void );
int     Psetuid( int id );
int     Pkill( int pid, int sig );
void    *Psignal( int sig, void *handler );
int     Pvfork( void );
int     Pgetgid( void );
int     Psetgid( int id );
long    Psigblock( long mask );
long    Psigsetmask( long mask );
long    Pusrval( long arg );
int     Pdomain( int newdom );
void    Psigreturn( void );
int     Pfork( void );
long    Pwait3( int flag, long *rusage );
int     Fselect( unsigned int timeout, long *rfds, long *wfds, long *xfds );
void    Prusage( long *r );
long    Psetlimit( int lim, long value );
long    Talarm( long secs );
void    Pause( void );
long    Sysconf( int n );
long    Psigpending( void );
long    Dpathconf( char *name, int n );
long    Pmsg( int mode, long mbox, MSG *msg );
long    Fmidipipe( int pid, int in, int out );
int     Prenice( int pid, int delta );
long    Dopendir( char *name, int flag );
long    Dreaddir( int buflen, long dir, char *buf );
long    Drewinddir( long dir );
long    Dclosedir( long dir );
long    Fxattr( int flag, char *name, XATTR *buf );
long    Flink( char *oldname, char *newname );
long    Fsymlink( char *oldname, char *newname );
long    Freadlink( int size, char *buf, char *name );
long    Dcntl( int cmd, char *name, long arg );
long    Fchown( char *name, int uid, int gid );
long    Fchmod( char *name, int mode );
long    Pumask( unsigned int mode );
long    Psemaphore( int mode, long id, long timeout );
long    Dlock( int mode, int drive );
void    Psigpause( unsigned long mask );
long    Psigaction( int sig, SIGACTION *act, SIGACTION *oact );
int     Pgeteuid( void );
int     Pgetegid( void );
#define VERTFLAG          0x0100
#define STMODES           0x0080
#define OVERSCAN          0x0040
#define PAL               0x0020
#define VGA               0x0010
#define TV                0x0000
#define COL80             0x08
#define COL40             0x00
#define BPS16             4
#define BPS8              3
#define BPS4              2
#define BPS2              1
#define BPS1              0
#define NUMCOLS           7
long    locksnd( void );
long    unlocksnd( void );
long    soundcmd( int mode, int data );
long    setbuffer( int reg, void *begaddr, void *endaddr );
long    setsndmode( int mode );
long    settracks( int playtracks, int rectracks );
long    setmontracks( int montrack );
long    setinterrupt( int src_inter, int cause );
long    buffoper( int mode );
long    dsptristate( int dspxmit, int dsprec );
long    gpio( int mode, int data );
long    devconnect( int src, int dst, int srcclk, int prescale,
                    int protocol );
long    sndstatus( int reset );
long    buffptr( long *ptr );
int     Dsp_LoadProg( char *file, int ability, char *buffer );
long    Dsp_LodToBinary( char *file, char *codeptr );
void    Dsp_DoBlock( char *data_in, long size_in, char *data_out,
                     long size_out );
void    Dsp_BlkHandShake( char *data_in, long size_in, char *data_out,
                          long size_out );
void    Dsp_BlkUnpacked( long *data_in, long size_in, long *data_out,
                         long size_out );
void    Dsp_InStream( char *data_in, long block_size, long num_blocks,
                      long *blocks_done );
void    Dsp_OutStream( char *data_out, long block_size, long num_blocks,
                       long *blocks_done );
void    Dsp_IOStream( char *data_in, char *data_out, long block_insize,
                      long block_outsize, long num_blocks,
                      long *blocks_done );
void    Dsp_RemoveInterrupts( int mask );
int     Dsp_GetWordSize( void );
int     Dsp_Lock( void );
void    Dsp_Unlock( void );
void    Dsp_Available( long *xavailable, long *yavailable );
int     Dsp_Reserve( long xreserve, long yreserve );
void    Dsp_ExecProg( char *codeptr, long codesize, int ability );
void    Dsp_ExecBoot( char *codeptr, long codesize, int ability );
void    Dsp_TriggerHC( int vector );
int     Dsp_RequestUniqueAbility( void );
int     Dsp_GetProgAbility( void );
void    Dsp_FlushSubroutines( void );
int     Dsp_LoadSubroutine( char *codeptr, long codesize, int ability );
int     Dsp_InqSubrAbility( int ability );
int     Dsp_RunSubroutine( int handle );
int     Dsp_Hf0( int flag );
int     Dsp_Hf1( int flag );
int     Dsp_Hf2( void );
int     Dsp_Hf3( void );
void    Dsp_BlkWords( void *data_in, long size_in, void *data_out,
                      long size_out );
void    Dsp_BlkBytes( void *data_in, long size_in, void *data_out,
                      long size_out );
char    Dsp_HStat( void );
void    Dsp_SetVectors( void (*receiver)( ), long (*transmitter)( ));
int     setmode( int modecode );
int     mon_type( void );
void    ext_sync( int flag );
