agranlund/raven/sw/rom/mon/hw/cpu.c

#include "hw/cpu.h"

#define VBR_PROXY_IN_ROM        1
#define PMMU_PAGESIZE           (4 * 1024UL)

extern NMIFunc_t   NMIFunc;
extern uint32_t    NMIBusy;

uint32_t*   vbrTable __attribute__((aligned(4)));
uint32_t*   mmuRootTable __attribute__((aligned(4)));
uint32_t*   mmuInvalidPtrTable __attribute__((aligned(4)));
uint32_t*   mmuInvalidPageTable __attribute__((aligned(4)));
uint32_t*   mmuInvalidPage __attribute__((aligned(4)));
uint32_t*   mmuInvalidPageDesc __attribute__((aligned(4)));


//-----------------------------------------------------------------------
// cpu
//-----------------------------------------------------------------------
void cpu_NullNMI(regs_t* r) {
}


bool cpu_Init()
{
    // set dummy nmi handler
    NMIFunc = cpu_NullNMI;
    NMIBusy = 0;

    uint32_t rev;
    cpu_Detect(&rev, 0);

    uint32_t pcr = 0;
    pcr |= (1 << 0);        // enable superscalar dispatch
    if ((rev == 1) || (rev == 5)) {
        pcr |= (1 << 5);    // disable store/load bypass (errata I14)
    }
    cpu_SetPCR(pcr);
    return true;
}


uint32_t cpu_Detect(uint32_t* revout, uint32_t* idout)
{
    uint32_t sku = CPU_UNKONWN;
    uint32_t rev = 1;

    uint32_t pcr = cpu_GetPCR();
    rev = (pcr >> 8) & 0xFF;
    if ((pcr & 0x000f0000) == 0)
        sku = CPU_68060;
    else if (rev == 4)
        sku = CPU_68LC060;
    else if (rev == 3)
        sku = CPU_68EC060;

    if (idout)
        *idout = pcr & 0xffffff00;

    if (revout)
        *revout = rev;

    return sku;
}


NMIFunc_t cpu_SetNMI(NMIFunc_t func)
{
    NMIFunc_t old = NMIFunc;
    NMIFunc = func;
    return old;
}


//-----------------------------------------------------------------------
// mmu
//-----------------------------------------------------------------------
uint32_t* mmu_Init(uint32_t unmapped_desc)
{
    mmuRootTable        = (uint32_t*) mem_LinearAlloc(128 * 4, 512);
    mmuInvalidPtrTable  = (uint32_t*) mem_LinearAlloc(128 * 4, 512);
    mmuInvalidPageTable = (uint32_t*) mem_LinearAlloc( 64 * 4, 256);
    mmuInvalidPageDesc  = (uint32_t*) mem_LinearAlloc(  1 * 4, 256);
    mmuInvalidPage      = (uint32_t*) mem_LinearAlloc(PMMU_PAGESIZE, PMMU_PAGESIZE);

    mmuInvalidPageDesc[0] = unmapped_desc ? unmapped_desc : (((uint32_t)mmuInvalidPage) | (PMMU_READWRITE | PMMU_CM_WRITETHROUGH));

    for (int i=0; i<PMMU_PAGESIZE/4; i++)
        mmuInvalidPage[i] = 0;

    for (int i=0; i<64; i++)
        mmuInvalidPageTable[i] = ((uint32_t)mmuInvalidPageDesc) | PMMU_INDIRECT;

    for (int i=0; i<128; i++)
        mmuInvalidPtrTable[i] = ((uint32_t)mmuInvalidPageTable) | PMMU_READWRITE;

    for (int i=0; i<128; i++)
        mmuRootTable[i] = ((uint32_t)mmuInvalidPtrTable) | PMMU_READWRITE;

    return mmuRootTable;
}


uint32_t* mmu_GetPageDescriptor(uint32_t log)
{
    const uint32_t ptrTableAddressMask = ~511UL;
    const uint32_t pageTableAddressMask = ~255UL;
    //const uint32_t pageAddressMask = ~(PMMU_PAGESIZE - 1);
    //uint32_t addr = log & ~(PMMU_PAGESIZE - 1);

    uint32_t rootIdx = (log >> 25) & 127;
    uint32_t ptrIdx  = (log >> 18) & 127;
    uint32_t pageIdx = (log >> 12) & 63;

    uint32_t* ptrTable = (uint32_t*) (mmuRootTable[rootIdx] & ptrTableAddressMask);
    if (ptrTable == mmuInvalidPtrTable) {
        ptrTable = (uint32_t*) mem_LinearAlloc(128 * 4, 512);
        for (int i=0; i<128; i++)
            ptrTable[i] = ((uint32_t)mmuInvalidPageTable) | PMMU_READWRITE;

        mmuRootTable[rootIdx] = ((uint32_t)ptrTable) | PMMU_READWRITE;
    }

    uint32_t* pageTable = (uint32_t*) (ptrTable[ptrIdx] & pageTableAddressMask);
    if (pageTable == mmuInvalidPageTable) {
        pageTable = (uint32_t*) mem_LinearAlloc(64 * 4, 256);
        for (int i=0; i<64; i++)
            pageTable[i] = ((uint32_t)mmuInvalidPageDesc) | PMMU_INDIRECT;
        ptrTable[ptrIdx] = ((uint32_t)pageTable) | PMMU_READWRITE;
    }

    return &pageTable[pageIdx];
}


void mmu_Map(uint32_t log, uint32_t phys, uint32_t size, uint32_t flags)
{
    const uint32_t pageAddressMask = ~(PMMU_PAGESIZE - 1);
    uint32_t end = (log + size + (PMMU_PAGESIZE - 1)) & pageAddressMask;
    uint32_t src = log & pageAddressMask;
    uint32_t dst = phys & pageAddressMask;

    while (src != end)
    {
        uint32_t* pageDescriptor = mmu_GetPageDescriptor(src);
        *pageDescriptor = flags | dst;
        src += PMMU_PAGESIZE;
        dst += PMMU_PAGESIZE;
    }
}


void mmu_Redirect(uint32_t logsrc, uint32_t logdst, uint32_t size)
{
    const uint32_t pageAddressMask = ~(PMMU_PAGESIZE - 1);
    uint32_t end = (logsrc + size + (PMMU_PAGESIZE - 1)) & pageAddressMask;
    uint32_t src = logsrc & pageAddressMask;
    uint32_t dst = logdst & pageAddressMask;

    while (src != end)
    {
        uint32_t* srcPageDescriptor = mmu_GetPageDescriptor(src);
        uint32_t* dstPageDescriptor = mmu_GetPageDescriptor(dst);
        *srcPageDescriptor = PMMU_INDIRECT | (uint32_t)dstPageDescriptor;
        src += PMMU_PAGESIZE;
        dst += PMMU_PAGESIZE;
    }
}

void mmu_Invalid(uint32_t log, uint32_t size)
{
    const uint32_t pageAddressMask = ~(PMMU_PAGESIZE - 1);
    uint32_t end = (log + size + (PMMU_PAGESIZE - 1)) & pageAddressMask;
    uint32_t src = log & pageAddressMask;

    while (src != end)
    {
        uint32_t* pageDescriptor = mmu_GetPageDescriptor(src);
        *pageDescriptor &= ~3UL;
        src += PMMU_PAGESIZE;
    }
}

// jmp ([0x08.w])  // 4ef0 01e1 0008
// jmp ([0x08.l])  // 4ef0 01f1 0000 0008

#if VBR_PROXY_IN_ROM
const uint16_t vbrProxy[] __attribute__((aligned(16))) = {
    0x4ef0, 0x01e1, 0x0000, 0x0000, 0x4ef0, 0x01e1, 0x0004, 0x0000, 0x4ef0, 0x01e1, 0x0008, 0x0000, 0x4ef0, 0x01e1, 0x000c, 0x0000,
    0x4ef0, 0x01e1, 0x0010, 0x0000, 0x4ef0, 0x01e1, 0x0014, 0x0000, 0x4ef0, 0x01e1, 0x0018, 0x0000, 0x4ef0, 0x01e1, 0x001c, 0x0000,
    0x4ef0, 0x01e1, 0x0020, 0x0000, 0x4ef0, 0x01e1, 0x0024, 0x0000, 0x4ef0, 0x01e1, 0x0028, 0x0000, 0x4ef0, 0x01e1, 0x002c, 0x0000,
    0x4ef0, 0x01e1, 0x0030, 0x0000, 0x4ef0, 0x01e1, 0x0034, 0x0000, 0x4ef0, 0x01e1, 0x0038, 0x0000, 0x4ef0, 0x01e1, 0x003c, 0x0000,
    0x4ef0, 0x01e1, 0x0040, 0x0000, 0x4ef0, 0x01e1, 0x0044, 0x0000, 0x4ef0, 0x01e1, 0x0048, 0x0000, 0x4ef0, 0x01e1, 0x004c, 0x0000,
    0x4ef0, 0x01e1, 0x0050, 0x0000, 0x4ef0, 0x01e1, 0x0054, 0x0000, 0x4ef0, 0x01e1, 0x0058, 0x0000, 0x4ef0, 0x01e1, 0x005c, 0x0000,
    0x4ef0, 0x01e1, 0x0060, 0x0000, 0x4ef0, 0x01e1, 0x0064, 0x0000, 0x4ef0, 0x01e1, 0x0068, 0x0000, 0x4ef0, 0x01e1, 0x006c, 0x0000,
    0x4ef0, 0x01e1, 0x0070, 0x0000, 0x4ef0, 0x01e1, 0x0074, 0x0000, 0x4ef0, 0x01e1, 0x0078, 0x0000, 0x4ef0, 0x01e1, 0x007c, 0x0000,
    0x4ef0, 0x01e1, 0x0080, 0x0000, 0x4ef0, 0x01e1, 0x0084, 0x0000, 0x4ef0, 0x01e1, 0x0088, 0x0000, 0x4ef0, 0x01e1, 0x008c, 0x0000,
    0x4ef0, 0x01e1, 0x0090, 0x0000, 0x4ef0, 0x01e1, 0x0094, 0x0000, 0x4ef0, 0x01e1, 0x0098, 0x0000, 0x4ef0, 0x01e1, 0x009c, 0x0000,
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
    0x4ef0, 0x01e1, 0x0270, 0x0000, 0x4ef0, 0x01e1, 0x0274, 0x0000, 0x4ef0, 0x01e1, 0x0278, 0x0000, 0x4ef0, 0x01e1, 0x027c, 0x0000,
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
};
#else
static uint16_t* vbrProxy;
#endif

bool vbr_Init()
{
    vbrTable = (uint32_t*) mem_LinearAlloc(256 * 4, 256);
#if VBR_PROXY_IN_ROM
    for (uint32_t i=0; i<256*4; i+=4) {
        vbr_Set(i, (uint32_t) &vbrProxy[i]);
    }
#else
    vbrProxy = (uint16_t*) mem_LinearAlloc(256 * 4 * 2, 256);
    for (uint32_t i=0, j=0; i<256*4; i+=4) {
        vbrProxy[j++] = 0x4ef0; // jmp ([addr.w])
        vbrProxy[j++] = 0x01e1;
        vbrProxy[j++] = (uint16_t)i;
        vbrProxy[j++] = 0x0000; // unused
        vbr_Set(i, (uint32_t) &vbrProxy[j-4]);
    }
#endif
    vbr_Set(0x60, (uint32_t) vecRTE); // IRQ0 : Spurious
    vbr_Set(0x7C, (uint32_t) vecNMI); // IRQ7 : NMI
    vbr_Apply();
    return true;
}

void vbr_Set(uint32_t vec, uint32_t addr)
{
    vbrTable[vec >> 2] = addr;
}

void vbr_Apply()
{
    cpu_SetVBR((uint32_t)vbrTable);
}


//-----------------------------------------------------------------------
// motorola support package
//
//  Installed to vbr proxy by defaults.
//  can be reinstalled to different table later by calling msp_Install
//
//  eg, rvbios.prg can call msp_Install(0) to put them in TOS vectors
//  so that some programs (mint1.16) which use unimpl instructions
//  to identify cpu can do so correctly.
//
//-----------------------------------------------------------------------
extern void cpu_InstallSP(uint32_t vbr);
extern void cpu_UninstallSP();

void msp_Install(uint32_t vbr) {
	static bool installed = false;
	uint32_t ipl = cpu_SetIPL(7);
	if (installed) {
		cpu_UninstallSP();
	}
	cpu_InstallSP(vbr);
    vbr_Apply();
    cpu_CacheFlush();
	installed = true;
	cpu_SetIPL(ipl);
}

bool msp_Init() {
    uint32_t vbr = cpu_GetVBR();
    if (vbr == 0) {
        return false;
    }
    msp_Install(vbr);
    return true;
}
