agranlund/raven/fw/eiffel/eiffel_1.10.2-raven.asm

; ********************************************************************************
; Filename: Eiffel.asm
; Date: July 18, 2001
; Update: November 27, 2004
; 
; Authors: Favard Laurent, Didier Mequignon
; 
; This program is free software; You can redistribute it and/or modify
; it under the terms of the gnu general public license as published by
; The Free Software Foundation; Either version 2 of the license, or
; (at your option) Any later version.
; 
; This program is distributed in the hope that it will be used,
; But within Any Warranty; Without Even the implied warranty of
; Merchantability or fitness for a particular purposes.  See The
; GNU General Public License for More Details.
; 
; You should have received a copy of the gnu general public license
; Along with this program; If not, Write to the Free Software
; Foundation, Inc., 59 temple place, suite 330, boston, ma 02111-1307 USA
; 
; ********************************************************************************
; Hardware Description:
; 
; Processor: 16F876
; Crystal: 4MHz
; WDT: Disable
; RS-232C: Max 232a Converter, TXD/RXD WIRED
; Power supply: via RJ-11 Cable/TXD, RXD
; Soft revision: 1.10
; Revision Board: C
; 
; ********************************************************************************
; Software note:
; 
; - Compatible with the pilot realizes by the OXO company.
; 
; - DEFAUT compatible with the Atari mouse protocol. The peak
; transforms the mouse mouse/2 frames into normal mouse atari,
; Whatever the branched mouse.
; 
; - Addition of additional scan-codes for Atari for the news
; PS/2 keys and new mouse functions.
; 
; See the /docs/xtensionatari.txt file
; 
; ********************************************************************************
; 
; This program makes it possible to translate the scan-codes of the game 3 (or 2
; From version 1.0.5) from a PS/2 keyboard to scan-codes
; Atari IKBD and to manage a standard or smart PS/2 mouse
; Roulette 3 buttons and double roulette 5 buttons. The pimples
; 4 and 5 are assigned to scan-codes.
; 
; The 2 original designed joysticks in the Atari IKBD can also
; Be connected (from version 1.0.4):
; The joystick 0 is branch on port A of the peak:
; RA1: High
; RA2: Bas
; RA3: Gauche
; RA4: Right
; RA5: shot
; The joystick 1 is branch on port C of the peak:
; RC0: High
; RC1: Bas
; RC2: left
; RC3: right
; RC4: shot
; 
; The control of a fan is also possible (from the version
; 1.0.4):
; RC5: Continuous engine control in all or nothing via a mosfet.
; RA0: Analog Entrance Temperature An0, a CTN 10kohms at 25
; deg is connected between an0 and vss (0V) with a reminder
; VDD (+4.3V) of 10kohms. Let Van0 = (4.3 * RCTN)/(10th+RCTN).
; Val_an0 = ADC value on year0 or 0 for 0V and 255 for 4.3V or:
; Val_an0 = (256 * RCTN)/(10th+RCTN)
; 
; The software allows the connection of the card to an RS-232C serie port
; Or directly to an Atari ST computer (RJ-12 or HE-14).
; 
; If the program is compile with LCD (since version 1.0.9), the
; Serial_debug is deleted and an LCD display takes its place in RB4/5
; HD44780 compatible by 2 bits RB4 and RB5 via a 74LS174. In that
; Case The Debug Jumpers who follow are unusable.
; 
; The two jumpers allow:
; 
; Jumper4, allowing to activate or not:
; 
; 5V on Portb4: Atari mode (Translation of keyboard/mouse codes)
; 0V on Portb4: direct mode (no translation, PS/2 direct)
; 
; Jumper 5, allowing to activate or not:
; 
; 5V on Portb5: normal mode (connection to an atari)
; 0V on Portb5: Debug mode (RS-232C connection)
; 
; normal debug
; 
; The Serie 9600 BPS transmission frequency 7812.5 BPS.
; The transmission of the Binary Ascii keyboard bytes.
; The transmission of binary ascii bytes.
; The emission of the text channel 'debug' no
; ********************************************************************************
; Notes:
; Crystal 4 MHz, BPS Rate for Atari = 7812.5
; BPS Rate for RS232 = 9600
; 
; Serial frame: 1 start bit, 8 bits data, 1 stop stop
; 
; JUMPER4 = PIN 4 Port B (Disable State at 5v with Pull-up)
; JUMPER5 = PIN 5 Port B (Disable State at 5v with Pull-up)
; LED GREEN = PIN 6 Port B (Enable State at 0V)
; LED Yellow = PIN 7 Port B (Enable State at 0V)
; ********************************************************************************
; See the Technik.txt and Evolution.txt file
; ********************************************************************************


; ********************************************************************************
; 1.10.2-RAVEN
; - Comments translated to english by google translate
; - Default to scancode set 2 instead of rarely used set 3
; - can be built with ansi layout as default
; - can be built to communicate with high baud rate
; ********************************************************************************


		PROCESSOR p16f876a
		RADIX dec
		
#include <p16f876a.inc>					; Processor Specific Variable Definitions
#include <eiffel.inc>					; macros

		LIST      P=16F876A			; List Directive to Define Processor

		__CONFIG _CP_OFF & _DEBUG_OFF & _WRT_OFF & _CPD_OFF & _LVP_OFF & _BODEN_OFF & _PWRTE_ON & _WDT_OFF & _XT_OSC

; ----- Flags Compilation -------------------------------------------------------------------------------------

SERIAL_DEBUG                 EQU     0; If 0, Portb4 & Portb5 Enlevates, Atari mode only
                                      ; Leave 0 for Lyndon cards
SCROOL_LOCK_ERR              EQU     0; If 1, use to display errors Breakdown mouse PS/2
                                      ; On the SCROLL LOCK LED on the keyboard
NON_BLOQUANT                 EQU     1; If 1, PS/2 non-blocking routines (time-out)
PS2_ALTERNE                  EQU     1; If 1, alternate management keyboard and PS/2 mouse
LCD                          EQU     0; If 1, LCD display In place of the JYYSTICK 0 compatible HD44780
LCD_DEBUG                    EQU     0; If 1, LCD display uses to see the codes sent to Atari
INTERRUPTS                   EQU     1; If 1, Timer 2 Gere by interruptions => Need a residant 1.10


IF SERIAL_DEBUG
BAUDRATE                     EQU     BAUD_9600
ELIFNDEF BAUDRATE
BAUDRATE                     EQU     BAUD_7812_5
ENDIF


; ----- Variables --------------------------------------------------------------------------------------------

; page 0 (usable from 0x20)
Status_Boot                  EQU    0x20; Return to 0 to reset
Info_Boot                    EQU    0x21; Put to 0xff if the Demarre program on page 2 in flash
Val_AN0                      EQU    0x22; Reading CTN on An0
BUTTONS                      EQU    0x23; mouse buttons
OLD_BUTTONS                  EQU    0x24; Former state of mouse buttons
OLD_BUTTONS_ABS              EQU    0x25; Old state of mouse buttons in absolute mode
JOY0                         EQU    0x26; Joystick 0 reading 0
JOYB                         EQU    0x26; = Joy0, just to test eventually with Joy1
JOY1                         EQU    0x27; Reading Joystick 1
BUTTON_ACTION                EQU    0x28; IKBD button mode
Counter_MState_Temperature   EQU    0x29; Temperature reading machine (CPU load reduction)
RCTN                         EQU    0x2A; CTN / 100 resistance value
Idx_Temperature              EQU    0x2B; Index Reading Table Temperature by interpolation
Counter_LOAD                 EQU    0x2C; COMPTER CONTRES REPUSE by LOAD command in main loop
Counter_Debug_Lcd            EQU    0x2E

DEB_INDEX_EM                 EQU    0x38; Data index to send circular buffer Liaison Serie
FIN_INDEX_EM                 EQU    0x39; end index given to send circular buffer
PTRL_LOAD                    EQU    0x3A; Strong weight address LOAD
PTRH_LOAD                    EQU    0x3B; Low weight command LOAD
TEMP5                        EQU    0x3C
TEMP6                        EQU    0x3D
Flags4                       EQU    0x3E  
Flags5                       EQU    0x3F
HEADER_IKBD                  EQU    0x40; IKBD HOST IKBD
KEY_MOUSE_WHEEL              EQU    0x41; Movement scan-code (Wheel & Wheel+)
KEY2_MOUSE_WHEEL             EQU    0x42; Additional byte: scan-code button 4 or 5 (Wheel+)
CLIC_MOUSE_WHEEL             EQU    0x43; Supplementary byte: Central button scan
Value_0                      EQU    0x44; 1 byte reception trame mouse ps/2
Value_X                      EQU    0x45; 2nd byte Reception Motor mouse PS/2
Value_Y                      EQU    0x46; 3rd byte reception trame mouse ps/2
Value_Z                      EQU    0x47; 4th Event byte Reception Motor mouse PS/2
Counter_Mouse                EQU    0x48; COMPTER OCTET Reception Mot mouse PS/2
Temperature                  EQU    0x49; CTN temperature reading on year0
Rate_Joy                     EQU    0x4A; time monitoring joystick ikbd
Counter_5MS                  EQU    0x4B; clock clock and time base 5 ms
Counter_10MS_Joy_Monitor     EQU    0x4C; DELAIRS SEND MONITORING JYYSTICKS
Counter3                     EQU    0x4D; Boucles counter
Counter_10MS_Joy             EQU    0x4E; Keycode Joystick 0 (not 100 ms)
Counter_100MS_Joy            EQU    0x4F; 100 ms meter Keycode Joystick 0 mode
RX_JOY                       EQU    0x50; KEYCODE JOYSTICK 0 IKBD
RY_JOY                       EQU    0x51; Time Ry Mode Keycode Joystick 0 IKBD
TX_JOY                       EQU    0x52; time tx mode keycode joystick 0 ikbd
TY_JOY                       EQU    0x53; Ty mode KEYCODE JOYSTICK 0 IKBD
VX_JOY                       EQU    0x54; time vx fashion keycode joystick 0 ikbd
VY_JOY                       EQU    0x55; Time Vy Mode Keycode Joystick 0 IKBD
Status_Joy                   EQU    0x56; FLAGS JYYSTICK 0 mode Keycode
OLD_JOY                      EQU    0x57; Former state joystick buttons 0 fashion keycode
START_RX_JOY                 EQU    0x58; Tempo RX MODE start -up value KEYCODE JOYSTICK 0
START_RY_JOY                 EQU    0x59; Tempo RY MODE start -up value KEYCODE JOYSTICK 0
START_TX_JOY                 EQU    0x5A; Tempo TX MODE start -up value KEYCODE JOYSTICK 0
START_TY_JOY                 EQU    0x5B; DEMARrage Value Ty Mode Keycode JYYSTICK 0
X_SCALE                      EQU    0x5C; ABSOLLY MOUSED FASTER FASTER
Y_SCALE                      EQU    0x5D; A absolute mouse factor factor
X_POSH                       EQU    0x5E; ABSOLUE SOUS POSITION SOULD STRAY
X_POSL                       EQU    0x5F; ABSOLUE SOUS POSEMENT SOUS Low weight
Y_POSH                       EQU    0x60; ABSOLUE MOUSE POSIT
Y_POSL                       EQU    0x61; ABSOLUE MOUSE POST MOUSE Low weight
X_POSH_SCALED                EQU    0x62; absolute mouse x position with strong weight factor
X_POSL_SCALED                EQU    0x63; absolute mouse x position with low weight factor factor
Y_POSH_SCALED                EQU    0x64; ABSOLUE MOUSE POSEMENT WITH FORCE FORTOR
Y_POSL_SCALED                EQU    0x65; Absolute mouse position with low weight factor factor
X_MAX_POSH                   EQU    0x66; Absolute x position maximum mouse strong weight
X_MAX_POSL                   EQU    0x67; Absolute x position maximum mouse low weight
Y_MAX_POSH                   EQU    0x68; Absolute position maximum mouse strong weight
Y_MAX_POSL                   EQU    0x69; Absolute position maximum mice low weight
X_MOV                        EQU    0x6A; Relative DEPLACEMENT MOUSE IN X
Y_MOV                        EQU    0x6B; Deplacement Relative mouse in Y
X_INC_KEY                    EQU    0x6C; Keycode mouse in x mode
Y_INC_KEY                    EQU    0x6D; Keycode mouse in x mode
DELTA_X                      EQU    0x6E; Deltax mode Keycode mouse ikbd
DELTA_Y                      EQU    0x6F; Deltay mode Keycode mouse ikbd

; municipalities to all pages
TEMP3                        EQU    0x70
TEMP4                        EQU    0x71
Counter                      EQU    0x72; Boucles counter
Value                        EQU    0x73; OCTET received
TEMP1                        EQU    0x74
Counter2                     EQU    0x75; Boucles counter
PARITY                       EQU    0x76; PARE Scripture/PS/2 reading and flashing
TEMP2                        EQU    0x77
Flags                        EQU    0x78
Flags2                       EQU    0x79
Flags3                       EQU    0x7A
Counter_5MS_Inter            EQU    0x7B; inter, assignment to keep from Eiffel 1.10
Save_STATUS                  EQU    0x7C; inter, assignment to keep from Eiffel 1.10
Save_W                       EQU    0x7D; inter, assignment to keep from Eiffel 1.10
BUFFER_FLASH                 EQU    0x7E; Buffer 2 bytes

; Page 2 in zone not awarded 0 to reset by start_flash if <0x120
YEAR                         EQU    0x110; year, keep this order for the 6 clock variables
MONTH                        EQU    0x111; month
DAY                          EQU    0x112; day
HRS                          EQU    0x113; hours
MIN                          EQU    0x114; minutes
SEC                          EQU    0x115; seconds
YEAR_BCD                     EQU    0x116; year, keep this order for the 6 BCD variables
MONTH_BCD                    EQU    0x117; month
DAY_BCD                      EQU    0x118; day
HRS_BCD                      EQU    0x119; hours
MIN_BCD                      EQU    0x11A; minutes
SEC_BCD                      EQU    0x11B; seconds

USER_LCD                     EQU    0x120; Message 8 CHARACTERS LCD

; Page 3 in zone not awarded 0 to reset by start_flash if <0x1a0
TAMPON_EM                    EQU    0x190; Circular Buffer Serie connection (size_tampon_em in eiffel.inc)

; ----- Program ---------------------------------------------------------

		ORG	0x000
		
		clrf Status_Boot; Discount at 0 when switching or reset hard
Reset_Prog
		bsf PCLATH,3; Page 1 (0x800 - 0xfff)
		bcf PCLATH,4
		goto Start_Flash; jump to the launch program of page 0 or 2

Inter
		btfss INTCON,PEIE; Peripheral interrupt enable is 1 during the interruption
		                 ; So we jump the goto
; -----------------------------------------------------------------
; Startup, initialization (jump here after the boot!)
; Passage requires for interruptions from Eiffel 1.10
; -----------------------------------------------------------------
Startup
			goto Startup2		
		movwf Save_W; backup of w
		swapf STATUS,W
		clrf STATUS; page 0
		movwf Save_STATUS; backup of status
		bcf PIR1,TMR2IF; Acquitta Timer 2
		incf Counter_5MS_Inter,F
		swapf Save_STATUS,W; restitution of W and status
		movwf STATUS
		swapf Save_W,F
		swapf Save_W,W
		retfie
	
Startup2
		bsf PCLATH,3; Page 1 or 3 (0x800 - 0xfff)
		call Init
		bcf PCLATH,3; page 0 or 2
		goto Init_Flags

; -----------------------------------------------------------------
; Welcome characteristics! (Test on the CT60)
; -----------------------------------------------------------------

IF SERIAL_DEBUG
WelcomeText
		addwf PCL,F
		DT "Eiffel 1.10"
		IF INTERRUPTS
		DT "i"
		ENDIF
		DT" 11/2004"
		DT 0
ENDIF


; -------------------------------------------------------------------
; Main custom -waiting loop:
; We look at if a keyboard is arrived, then mouse
; -------------------------------------------------------------------

Main
		; ------------------------------------------------------------------------------
		; Waiting loop on clocks: Polling on KCLC and MCLK
		; Then blocking opposes and call for the treatment of element
		IF INTERRUPTS
		bsf INTCON,GIE; Authorizes interruptions
		ENDIF
		IF PS2_ALTERNE
		movf Counter_5MS,W
		andlw 3 	
		btfss STATUS,Z; Alternate management every 5 ms keyboard and 15 ms PS/2 mouse
			goto EnableMouse
		ENABLEKEYB
		goto Main_Loop
EnableMouse
		ENABLEMOUSE
		ELSE
		ENABLEPS2; Authorizes keyboard and mouse transfers at the same time
		ENDIF
Main_Loop
			IF PS2_ALTERNE	
			movf Counter_5MS,W
			andlw 3 	
			btfss STATUS,Z; Alternate management every 5 ms keyboard and 15 ms PS/2 mouse
				goto TstMouse; mouse management
			btfsc PORTB,KCLOCK; Clk's descending front
				goto TstAtariSend
			ELSE
			btfsc PORTB,KCLOCK; Clk's descending front
				goto TstMouse; The keyboard does not manifest itself, we go to the mouse
			ENDIF
			IF INTERRUPTS
			bcf INTCON,GIE; prohibited interruptions
			ENDIF
			DISABLEMOUSE; Block mouse
			call KPSGet2; => Value, we recover the keyboard byte
			goto doKeyboard; We call the complete keyboard treatment
TstMouse
			btfsc PORTB,MCLOCK; Clk's descending front
				goto TstAtariSend; The mouse does not manifest itself, we go into control control Atari
			IF INTERRUPTS
			bcf INTCON,GIE; prohibited interruptions
			ENDIF
			DISABLEKEYB; keyboard block
			call MPSGet2; => Value, we recover the byte mouse
			goto doMouse; We call the complete mouse treatment
TstAtariSend
			btfss Flags2,DATATOSEND
				goto TstAtariReceive; Nothing to be sent by the Serie Liaison
	 		btfss PIR1,TXIF; check that buffer is empty
				goto TstAtariReceive; full emission register
			DISABLEPS2; Block keyboard and mouse
			movf DEB_INDEX_EM,W; Circular buffer test
			subwf FIN_INDEX_EM,W
			btfss STATUS,Z
				goto SendData; End_index_em <> deb_index_em
			bcf Flags2,DATATOSEND
			goto Main
SendData
			bsf STATUS,IRP; page 3
			incf DEB_INDEX_EM,W; increment circular buffer data sent
			movwf FSR; Index pointer
			movlw TAILLE_TAMPON_EM
			subwf FSR,W
			btfsc STATUS,C
				clrf FSR; circular buffer
			movf FSR,W
			movwf DEB_INDEX_EM
			movlw LOW TAMPON_EM
			addwf FSR,F; Index pointer
			movf INDF,W; Reading in the stamp
			movwf TXREG; Transmit byte
			goto Main
TstAtariReceive
			btfss PIR1,RCIF; Control control Atari arrival
				goto TstTimer; Reception asynchronous connection
			DISABLEPS2; Block keyboard and mouse
			btfss RCSTA,OERR
				goto FramingErrorTest
			bcf RCSTA,CREN; Overrun Error
			bsf RCSTA,CREN; Enable reception
			goto Main
FramingErrorTest
			btfss RCSTA,FERR 
				goto ReceiveOK
			movf RCREG,W; Acquitta Framing Error error
			goto Main
ReceiveOK
			movf RCREG,W; Get Received Data Into W
			movwf Value; => Value, we test the Atari keyboard commands
			btfss Flags3,RE_TIMER_IKBD
				goto doAtariCommand; Treat the Atari Clavier Collection command
			call Receive_Bytes_Load				
			goto Main	
TstTimer
		IF !INTERRUPTS
			btfss PIR1,TMR2IF
                ELSE
                	movf Counter_5MS_Inter,W
                	subwf Counter_5MS,W
			btfsc STATUS,Z
		ENDIF
			goto Main_Loop
				
; -----------------------------------------------------------------
; Timer management 2 to 5 ms
; -----------------------------------------------------------------

doTimer
		DISABLEPS2; Block keyboard and mouse
		IF !INTERRUPTS
		bcf PIR1,TMR2IF; Acquitta Timer 2
		incf Counter_5MS,F
		movlw 200
		subwf Counter_5MS,W		
		btfss STATUS,Z
			goto NotIncClock
		clrf Counter_5MS
		ELSE
		bcf INTCON,GIE; prohibited interruptions
		movlw 200
		subwf Counter_5MS_Inter,W; Counter_5ms_inter - 200
		btfss STATUS,C
			goto NotIncClockInt; Counter_5ms_inter <200
		movwf Counter_5MS_Inter
		movwf Counter_5MS			
		bsf INTCON,GIE; Authorizes interruptions
		ENDIF
		bsf PCLATH,3; Page 1 or 3 (0x800 - 0xfff)
		call Inc_Clock; clock incorrect every second
		IF LCD
		IF !LCD_DEBUG
		call Time_Lcd
		call Temperature_Lcd
		ENDIF
		ENDIF
		bcf PCLATH,3; page 0 or 2
		movlw 1
		movwf Counter_MState_Temperature; launches the reading of the temperature
		btfss Flags2,RESET_KEYB
			goto NotResetKeyb
		bcf Flags2,RESET_KEYB; Flag Request Reset Keyboard given to 0
		call KbBAT; Preferable to cmdresetkey with certain keyboards
		movlw 0xF0; Return Code Reset keyboard
		call SerialTransmit_Host
                goto NotIncClock
                IF INTERRUPTS    
NotIncClockInt
		movf Counter_5MS_Inter,W
		movwf Counter_5MS		
		bsf INTCON,GIE; Authorizes interruptions
                goto NotIncClock
		ENDIF
NotResetKeyb		
		btfss Flags2,RESET_MOUSE
			goto NotIncClock
		call cmdResetMouse
NotIncClock
		bsf PCLATH,3; Page 1 or 3 (0x800 - 0xfff)
		call Read_Temperature; Temperature reading every second via counter_mstate_temperature
		bcf PCLATH,3; page 0 or 2
		btfsc Counter_5MS,0
			goto Main

; -----------------------------------------------------------------
; LCD management every 10 ms
; -----------------------------------------------------------------

		IF LCD
		IF !LCD_DEBUG
		btfss Flags4,LCD_ENABLE; LCD Timer Management inhibits
			goto Joysticks_10MS
		bsf PCLATH,3; Page 1 or 3 (0x800 - 0xfff)
		call Message_User_Lcd
		bcf PCLATH,3; page 0 or 2
		ENDIF
		ENDIF      

; -----------------------------------------------------------------
; Management under Timer 2 every 10 ms of the joysticks
; -----------------------------------------------------------------

Joysticks_10MS		
		btfss Flags,JOY_ENABLE; Management by Timer Joysticks
			goto Main; No joystick management
		btfsc Flags2,JOY_MONITOR
			goto Joy_Monitoring; Joystick monitoring
		btfsc Flags2,JOY_EVENT
			goto Not_100MS; Joysticks events
		btfss Flags2,JOY_KEYS; Shipping items
			goto Main; Nothing to manage under the timer at the joysticks
		decfsz Counter_10MS_Joy,F
			goto Not_100MS
		movlw 10
		movwf Counter_10MS_Joy
		incf Counter_100MS_Joy,F
		call SendAtariJoysticks_Fleches; KEYCODE MODE OF THE JOYSTICK 0
Not_100MS
		comf PORTA,W; management events joysticks or Keycode Action on Fire
		movwf TEMP1
		rrf TEMP1,W
		andlw 0x1F; 000FDGBH (fire, right, left, stocking, high)
		movwf TEMP1
		subwf JOY0,W; Joystick 0 reading 0
		btfsc STATUS,Z
			goto Not_Joy0_Change; No change joystick 0
		movf TEMP1,W		
		movwf JOY0; Joystick 0 reading 0
		movlw HEADER_JOYSTICK0; Header Joystick 0
		goto SerialTransmit_Joy
Not_Joy0_Change
		comf PORTC,W
		andlw 0x1F; 000FDGBH (fire, right, left, stocking, high)
		movwf TEMP1
		subwf JOY1,W; Reading Joystick 1
		btfsc STATUS,Z
			goto Main; No change joystick 1
		movf TEMP1,W	
		movwf JOY1; Reading Joystick 1
		movlw HEADER_JOYSTICK1; Header Joystick 1
SerialTransmit_Joy
		movwf HEADER_IKBD
		call Leds_Eiffel_On
		call SendAtariJoysticks
		goto End_Read
		
; -----------------------------------------------------------------
; Management under Timer 2 every 10 ms Sending Translands Joystick continuously
; -----------------------------------------------------------------

Joy_Monitoring
		decfsz Counter_10MS_Joy_Monitor,F
			goto Main
		movf Rate_Joy,W
		movwf Counter_10MS_Joy_Monitor
		call Leds_Eiffel_On
		bsf PCLATH,3; Page 1 or 3 (0x800 - 0xfff)
		call Read_Joysticks
		bcf PCLATH,3; page 0 or 2
		clrf TEMP1
		btfsc JOY0,4; Joystick 0 button
			bsf TEMP1,1
		btfsc JOY1,4; Joytick 1 button
			bsf TEMP1,0
		movf TEMP1,W; 00000000xy with Y for Fire Joystick 1 and X for Fire Joystick 0
		call SerialTransmit_Host
		swapf JOY0,W; Joystick 0 reading 0
		andlw 0xF0; 4 bits of strong weight
		movwf TEMP1
		movf JOY1,W; Reading Joystick 1
		andlw 0x0F; DGBHDGBH (right, left, bottom, top)
		iorwf TEMP1,W; nnnnmmmm with M for the joystick 1 and n for the joystick 0
		call SerialTransmit_Host
		goto End_Read
		
; -----------------------------------------------------------------
; Atari collection keyboard command
; -----------------------------------------------------------------

doAtariCommand
		bsf Flags,IKBD_ENABLE; Authorized IKBD transfers
		bcf Flags2,JOY_MONITOR; Monitoring Joysticks Desactive
		; ------------------------------------------------------------------------------
		; Temperature
		movf Value,W
		sublw IKBD_GETTEMP; Temperature reading
		btfss STATUS,Z
			goto Not_Get_Temperature
		movlw HEADER_STATUS; State Header
		call SerialTransmit_Host
		movlw IKBD_GETTEMP
		call SerialTransmit_Host
		movf Temperature,W; temperature
		call SerialTransmit_Host
		movf Val_AN0,W; Reading CTN on An0
		call SerialTransmit_Host
		clrw
		btfsc PORTC,MOTORON
			movlw 1
		call SerialTransmit_Host
		movlw Tab_Temperature-EEProm+IDX_LEVELHTEMP
		call Lecture_EEProm
		call SerialTransmit_Host
		movlw Tab_Temperature-EEProm+IDX_LEVELLTEMP
		call Lecture_EEProm
		call SerialTransmit_Host
		movf RCTN,W; CTN / 100 resistance value
		call SerialTransmit_Host		
		goto Main		
Not_Get_Temperature
		movf Value,W
		sublw IKBD_PROGTEMP; Temperature threshold programming
		btfss STATUS,Z
			goto Not_Prog_Temperature
		clrf Val_AN0; Reading CTN on AN0 => Update the measurement and control of the fan
		call SerialReceive; Temperature programming code
		sublw IDX_TAB_CTN+24; subtract the Max offset
		btfss STATUS,C; If carry = 1 no problem we go
			goto Not_Prog_EEProm; ignore code> idx_tab_ctn+24
		movf Value,W
		addlw Tab_Temperature-EEProm; To point the beginning of the temperature bytes in the table
		goto Prog_EEProm
Not_Prog_Temperature
		; ------------------------------------------------------------------------------
		; Programming mouse and keyboard
		movf Value,W
		sublw IKBD_PROGMS; Mouse programming
		btfss STATUS,Z
			goto Not_Prog_Mouse
		; Indicate the ignition programming mode of the three LEDs
		movlw LEDS_ON
		call cmdLedOnOff
		call SerialReceive; Mouse Programming Code
		sublw IDX_WHREPEAT; subtract the Max offset
		btfss STATUS,C; If carry = 1 no problem we go
			goto Not_Prog_EEProm; ignore code> idx_whrepeat
		movf Value,W
		addlw Tab_Mouse-EEProm; To point the beginning of the bytes mouse in the table
		goto Prog_EEProm
Not_Prog_Mouse
		movf Value,W
		sublw IKBD_PROGKB; Keyboard programming
		btfss STATUS,Z
			goto Not_ProgKB
		; Indicate the ignition programming mode of the three LEDs
		movlw LEDS_ON
		call cmdLedOnOff
		call SerialReceive; keyboard programming code
		comf Value,W		
		btfsc STATUS,Z
			goto ChangeSet; 0xff
		movf Value,W		
		sublw MAX_VALUE_LOOKUP; subtract the Max offset
		btfss STATUS,C; If carry = 1 no problem we go
			goto Not_Prog_EEProm; ignore code> max_value_lookup
		movf Value,W
		addlw Tab_Scan_Codes-EEProm; To point the start of the keyboard bytes in the table
		goto Prog_EEProm
ChangeSet
		movlw Tab_Config-EEProm
Prog_EEProm
		movwf Counter
		call SerialReceive
		WREEPROM Counter,Value
		goto Main
Not_ProgKB
		; ------------------------------------------------------------------------------
		; IKBD mouse operating mode
		movf Value,W
		sublw IKBD_SET_MOUSE_BUTTON_ACTION; Mouse buttons
		btfss STATUS,Z
			goto Not_Set_Mouse_Button_Action
		call SerialReceive
		movwf BUTTON_ACTION
		goto Main
Not_Set_Mouse_Button_Action
		movf Value,W
		sublw IKBD_REL_MOUSE_POS_REPORT; Relative fashion mouse
		btfss STATUS,Z
			goto Not_Rel_Mouse
		bcf Flags2,MOUSE_KEYS
		bcf Flags,MOUSE_ABS
		goto Mouse_Enable
Not_Rel_Mouse
		movf Value,W
		sublw IKBD_ABS_MOUSE_POSITIONING; Absolute fashion mouse
		btfss STATUS,Z
			goto Not_Abs_Mouse
		call SerialReceive; Xmsb, x maximum
		movwf X_MAX_POSH; Absolute x position maximum mouse strong weight
		call SerialReceive; Xlsb
		movwf X_MAX_POSL; Absolute X position maximum mouse low weight
		call SerialReceive; YMSB, Y Maximum
		movwf Y_MAX_POSH; ABSOLUE Position Maximum Mouse Strong Weight
		call SerialReceive; Ylsb
		movwf Y_MAX_POSL; ABSOLUE MOUSE MOUNDUE Position Low weight
		call Init_X_Y_Abs
		bcf Flags2,MOUSE_KEYS
		bsf Flags,MOUSE_ABS
		goto Mouse_Enable
Not_Abs_Mouse
		movf Value,W
		sublw IKBD_SET_MOUSE_KEYCODE_CODE; Mouse flucing touches mode
		btfss STATUS,Z
			goto Not_Mouse_KeyCode
		call SerialReceive; deltax
		call Change_0_To_1
		movwf DELTA_X; Deltax mode Keycode mouse ikbd
		call SerialReceive; deltay
		call Change_0_To_1
		movwf DELTA_Y; Deltay mode Keycode mouse ikbd
		clrf X_INC_KEY; Keycode mouse in x mode
		clrf Y_INC_KEY; Interect in Yeycode Mouse mode
		bsf Flags2,MOUSE_KEYS
		goto Mouse_Enable
Not_Mouse_KeyCode
		movf Value,W
		sublw IKBD_SET_MOUSE_THRESHOLD; unparalleled
		btfsc STATUS,Z
			goto Receive2Bytes; X & y Threshold
		movf Value,W
		sublw IKBD_SET_MOUSE_SCALE; Absolute Mouse Mouse Factor
		btfss STATUS,Z
			goto Not_Mouse_Scale
		call SerialReceive; X
		call Change_0_To_1
		movwf X_SCALE
		call SerialReceive; Y
		call Change_0_To_1
		movwf Y_SCALE
		goto Conv_Not_Scaled
Not_Mouse_Scale
		movf Value,W
		sublw IKBD_INTERROGATE_MOUSE_POS; Request absolute position mouse
		btfss STATUS,Z
			goto Not_Mouse_Pos
		btfss Flags,MOUSE_ABS
			goto Main; <> Absolute fashion
		btfsc Flags2,JOY_MONITOR
			goto Main
		movlw HEADER_ABSOLUTE_MOUSE; Header mouse absolute fashion
		movwf HEADER_IKBD
		bcf PORTB,LEDYELLOW; Led mouse lighter
		call SendAtariMouse
		bsf PORTB,LEDYELLOW; Eteint Led mouse
		goto Main
Not_Mouse_Pos
		movf Value,W
		sublw IKBD_LOAD_MOUSE_POS; Initialization absolute mouse coords
		btfss STATUS,Z
			goto Not_Load_Mouse_Pos
		call SerialReceive; 0
		call SerialReceive; Xmsb, x coordinates
		movwf X_POSH_SCALED; absolute mouse x position with strong weight factor
		call SerialReceive; Xlsb
		movwf X_POSL_SCALED; absolute mouse x position with low weight factor factor
		call SerialReceive; Ymsb, y coordinates
		movwf Y_POSH_SCALED; ABSOLUE MOUSE POSEMENT WITH FORCE FORTOR
		call SerialReceive; Ylsb
		movwf Y_POSL_SCALED; Absolute mouse position with low weight factor factor
Conv_Not_Scaled
		bsf PCLATH,3; Page 1 or 3 (0x800 - 0xfff)
		call Conv_Inv_Scale_X
		call Conv_Inv_Scale_Y
		bcf PCLATH,3; page 0 or 2
		goto Main
Not_Load_Mouse_Pos
		movf Value,W
		sublw IKBD_SET_Y0_AT_BOTTOM; 0 mouse below
		btfss STATUS,Z
			goto Not_Y0_At_Bottom
		bsf Flags,SIGN_Y
		goto Main
Not_Y0_At_Bottom
		movf Value,W
		sublw IKBD_SET_Y0_AT_TOP; 0 mouse at the top (out of default)
		btfss STATUS,Z
			goto Not_Y0_At_Top
		bcf Flags,SIGN_Y
		goto Main
Not_Y0_At_Top
		movf Value,W
		sublw IKDB_RESUME; Transfer authorization
		btfss STATUS,Z
			goto Not_Resume
		goto Main
Not_Resume
		movf Value,W
		sublw IKDB_DISABLE_MOUSE; Inhibit the mouse
		btfss STATUS,Z
			goto Not_Disable_Mouse
		bcf Flags,MOUSE_ENABLE
		goto Main
Not_Disable_Mouse
		movf Value,W
		sublw IKDB_PAUSE_OUTPUT; Transfers stop
		btfss STATUS,Z
			goto Not_Pause
		bcf Flags,IKBD_ENABLE
		goto Main
Not_Pause
		; ------------------------------------------------------------------------------
		; IKBD Joysticks operating mode
		movf Value,W
		sublw IKBD_SET_JOY_EVNT_REPORT; Joystick Automatic Transfers
		btfss STATUS,Z
			goto Not_Joy_On
		bcf Flags2,JOY_KEYS
		bsf Flags2,JOY_EVENT
		bsf Flags,JOY_ENABLE
		goto Main
Not_Joy_On
		movf Value,W
		sublw IKBD_SET_JOY_INTERROG_MODE; Automatic joystick transfers stop
		btfss STATUS,Z
			goto Not_Joy_Off
		bcf Flags2,JOY_KEYS
		bcf Flags2,JOY_EVENT
		bsf Flags,JOY_ENABLE
		goto Main
Not_Joy_Off
		movf Value,W
		sublw IKBD_JOY_INTERROG; Question Joysticks
		btfss STATUS,Z
			goto Not_Joy_Interrog
		btfss Flags,JOY_ENABLE
			goto Main; inhibited joysticks
		btfsc Flags2,JOY_KEYS
			goto Main; Keycode Joystick 0 mode
		btfsc Flags2,JOY_MONITOR
			goto Main; monitoring joysticks mode
		comf PORTA,W
		movwf JOY0
		rrf JOY0,W
		andlw 0x1F
		movwf JOY0; 000FDGBH (Fire, right, left, stocking, top) JYYSTICK 0
		comf PORTC,W
		andlw 0x1F
		movwf JOY1; 000FDGBH (Fire, right, left, stocking, top) Joystick 1
		movlw HEADER_JOYSTICKS; Header Joysticks
		goto SerialTransmit_Joy
Not_Joy_Interrog
		movf Value,W
		sublw IKBD_SET_JOY_MONITOR
		btfss STATUS,Z
			goto Not_Joy_Monitor; continuous joystick reading
		call SerialReceive; missed
		call Change_0_To_1
		movwf Rate_Joy
		movwf Counter_10MS_Joy_Monitor
		bsf Flags2,JOY_MONITOR
		bsf Flags,JOY_ENABLE
		goto Main
Not_Joy_Monitor
		movf Value,W
		sublw IKBD_SET_FIRE_BUTTON_MONITOR
		btfss STATUS,Z
			goto Not_Fire_Button
		goto Main
Not_Fire_Button
		movf Value,W
		sublw IKBD_SET_JOY_KEYCODE_MODE; Joystick 0 hits
		btfss STATUS,Z
			goto Not_Joy_KeyCode
		call SerialReceive; Rx
		movwf RX_JOY
		call SerialReceive; Ry
		movwf RY_JOY
		call SerialReceive; Tx
		movwf TX_JOY
		call SerialReceive; Ty
		movwf TY_JOY
		call SerialReceive; Vx
		movwf VX_JOY
		call SerialReceive; Vy
		movwf VY_JOY
		clrf Status_Joy
		movlw 0xFF
		movwf OLD_JOY
		bsf Flags2,JOY_KEYS
		bcf Flags2,JOY_EVENT
		bsf Flags,JOY_ENABLE
		goto Main
Not_Joy_KeyCode
		movf Value,W
		sublw IKDB_DISABLE_JOYSTICKS; Inhibit joysticks
		btfss STATUS,Z
			goto Not_Disable_Joysticks
		bcf Flags,JOY_ENABLE
		goto Main
Not_Disable_Joysticks
		movf Value,W
		sublw IKBD_TIME_OF_DAY_CLOCK_SET; Initializes the clock
		btfss STATUS,Z
			goto Not_Time_Set
		; ------------------------------------------------------------------------------
		; IKBD clock programming
		movlw LOW YEAR_BCD
		movwf FSR
		movlw 6
		movwf Counter
Loop_Get_Time
			call SerialReceive; YY, MM, DD, HH, MM, SS
			bsf STATUS,IRP; Page 2
			movwf INDF
			incf FSR,F
			decfsz Counter,F
		goto Loop_Get_Time
		clrf Counter_5MS
		bsf PCLATH,3; Page 1 or 3 (0x800 - 0xfff)
		call Conv_Inv_Bcd_Time
		bcf PCLATH,3; page 0 or 2
		goto Main
Not_Time_Set
		movf Value,W
		sublw IKBD_INTERROG_TIME_OF_DAY; clock
		btfss STATUS,Z
			goto Not_Interrog_Time
		; ------------------------------------------------------------------------------
		; IKBD clock reading
		call Leds_Eiffel_On
		call SendAtariClock
		goto End_Read
Not_Interrog_Time
		movf Value,W
		sublw IKBD_MEMORY_LOAD; MEMORY loading
		btfss STATUS,Z
			goto Not_Memory_Load
		; ------------------------------------------------------------------------------
		; Memory loading possible of
		; $ 00A0 A $ 00EF, and $ 0120 A $ 016F
		; If the basic address of the order and the number of byte are 0
		; => Flash programming on page 2 ($ 1000 A $ 1FFF) Motorola format
		call SerialReceive
		movwf PTRH_LOAD; Adrmsb
		call SerialReceive
		movwf PTRL_LOAD; Adrlsb
		call SerialReceive
		movwf Counter_LOAD; Num
		iorwf PTRL_LOAD,W; Adrlsb
		iorwf PTRH_LOAD,W; Adrmsb
		btfsc STATUS,Z
			goto Prog_Flash; Address $ 0000 size $ 00 => Flash programming
		bsf Flags3,RE_TIMER_IKBD; Flag reception ikbd in main loop
		goto Main
Prog_Flash
		; Indicate the ignition programming mode of the three LEDs
	 	movlw LEDS_ON
		call cmdLedOnOff
		call cmdDisableKey
		call cmdDisableMouse
		clrf STATUS; Correct Bug Init_Page Ram before Eiffel 1.10 (IRP = 0)
		bsf PCLATH,3; Page 1 (0x800 - 0xfff) Flashing program
		bcf PCLATH,4
		goto Ecriture_Flash
Not_Memory_Load
		movf Value,W
		sublw IKBD_MEMORY_READ; Memory reading
		btfss STATUS,Z
			goto Not_Memory_Read
		; ------------------------------------------------------------------------------
		; Memory reading possible everywhere
		; from $ 0000 to $ 01FF (PIC and RAM registers)
		; from $ 2100 to $ 20ff (EEPROM)
		; $ 8000 to $ ffff (to see the whole flash from $ 0000 to $ 1FFF
		; byte by byte in Motorola format)
		call SerialReceive
		movwf TEMP1; Adrmsb
		bcf STATUS,IRP; 0-1 pages
		btfsc Value,0; Adrmsb
			bsf STATUS,IRP; 2-3 pages
		call SerialReceive
		movwf Counter2
		movwf FSR; Adrlsb
		call Leds_Eiffel_On
		movlw HEADER_STATUS; State Header
		call SerialTransmit_Host
		movlw IKBD_MEMORY_LOAD; memory
		call SerialTransmit_Host
		btfsc TEMP1,7
			goto Dump_Flash; Flash reading if address> = 0x8000
		movlw 6; 6 bytes
		movwf Counter
		movf TEMP1,W
		sublw 0x21
		btfsc STATUS,Z
			goto Dump_EEProm; Reading Eeprom if address 0x21xx
Loop_Dump_Ram
			movf INDF,W
			call SerialTransmit_Host; data
			incf FSR,F
			btfsc STATUS,Z
				bsf STATUS,IRP; 2-3 pages
			decfsz Counter,F
		goto Loop_Dump_Ram	
		goto End_Read
Dump_EEProm
			movf Counter2,W
			call Lecture_EEProm
			call SerialTransmit_Host; data
			incf Counter2,F
			decfsz Counter,F
		goto Dump_EEProm	
		goto End_Read
Dump_Flash
		bcf TEMP1,7; Flash address strong weight
		movlw 3; 3 words (6 bytes)
		movwf Counter	
Loop_Dump_Flash
			READ_FLASH TEMP1,Counter2,BUFFER_FLASH; Reading 2 bytes
			movf BUFFER_FLASH+1,W
			call SerialTransmit_Host; Data Weight Low
			movf BUFFER_FLASH,W
			call SerialTransmit_Host; Data strong weight
			incf Counter2,F
			btfsc STATUS,Z
				incf TEMP1,F
			decfsz Counter,F
		goto Loop_Dump_Flash
End_Read
		call Leds_Eiffel_Off
		goto Main
Not_Memory_Read
		movf Value,W
		sublw IKBD_CONTROLLER_EXECUTE; unparalleled
		btfss STATUS,Z
			goto Not_Execute
Receive2Bytes
		call SerialReceive; Adrmsb
		; Adrlsb
Not_Prog_EEProm
		call SerialReceive
		goto Main
Not_Execute
		; ------------------------------------------------------------------------------
		; LCD display
		IF LCD
		IF !LCD_DEBUG
		movf Value,W
		sublw IKBD_LCD; Shipping or data to the LCD
		btfss STATUS,Z
			goto Not_Lcd
		call SerialReceive
                btfss STATUS,Z
                	goto Test_Data_Lcd; <> 0
		call SerialReceive
		bsf PCLATH,3; Page 1 or 3 (0x800 - 0xfff)
		call SendINS
		bcf PCLATH,3; page 0 or 2
		bcf Flags4,LCD_ENABLE; Inhibitory LCD Timer Management
		goto Main
Test_Data_Lcd
		movwf Counter_LOAD; number of bytes
		comf Counter_LOAD,W		
		btfss STATUS,Z
			goto Data_Lcd; <> 0xff
		bsf Flags4,LCD_ENABLE; Authorizes Timer Management LCD
		goto Not_Prog_EEProm; last byte
Data_Lcd
		bsf Flags4,RE_LCD_IKBD; Flag reception LCD
		bsf Flags3,RE_TIMER_IKBD; Flag reception ikbd in main loop
		goto Main		
Not_Lcd
		ENDIF
		ENDIF
		movf Value,W
		sublw IKBD_RESET; reset
		btfss STATUS,Z
			goto Not_Reset
		call SerialReceive
		sublw 1; Reset code
		btfss STATUS,Z
			goto Main
		; ------------------------------------------------------------------------------
		; Reset command => Eiffel Reset
		; - The CAPS indicator is canceled in the state word.
		; - We stop the events and PS/2 keyboard.
		; - We send the Reset command to the keyboard and to the PS/2 mouse.
		; - We authorize IKBD, mouse and joystick transfers.
		clrf Flags
		clrf Flags2
		clrf Flags3
		clrf Flags4
		clrf Flags5
		clrf Status_Joy
		clrf DEB_INDEX_EM; Data index to send circular buffer Liaison Serie
		clrf FIN_INDEX_EM; end index given to send circular buffer
		bcf PORTC,MOTORON; Fan stop
		call Leds_Eiffel_On
		IF LCD
		bsf PCLATH,3; Page 1 or 3 (0x800 - 0xfff)
		call Init_Lcd
		bcf PCLATH,3; page 0 or 2
		ENDIF
		btfss Status_Boot,POWERUP_MOUSE
			goto NotResetMouse
		call cmdDisableMouse
		bsf Flags2,RESET_MOUSE; Valid reset mouse in Timer Treatment
NotResetMouse
		btfss Status_Boot,POWERUP_KEYB
			goto Init_Flags
		movlw LEDS_ON
		call cmdLedOnOff
		bsf Flags2,RESET_KEYB; valid reset keyboard in timer treatment
Init_Flags
		call Init_X_Y_Abs; Absolute position mouse
		movlw Tab_Config-EEProm
		call Lecture_EEProm
		sublw 2; game 2 keyboard request
		btfsc STATUS,Z
			bsf Flags3,KEYB_SET_2
		IF LCD
		IF !LCD_DEBUG
		bsf PCLATH,3; Page 1 or 3 (0x800 - 0xfff)
		call Init_Message_User_Lcd
		bcf PCLATH,3; page 0 or 2
		bsf Flags4,LCD_ENABLE; Authorizes Timer Management LCD
		ENDIF
		ENDIF
		bsf Flags2,JOY_EVENT
		bsf Flags,JOY_ENABLE
		bsf Flags,IKBD_ENABLE
Mouse_Enable
		bsf Flags,MOUSE_ENABLE
		goto Main
Not_Reset
		; ------------------------------------------------------------------------------
		; Status commands
		movf Value,W
		sublw IKBD_STATUS_MOUSE_BUT_ACTION; status
		btfss STATUS,Z
			goto Not_Mouse_Action
		movlw HEADER_STATUS; State Header
		call SerialTransmit_Host
		movlw IKBD_SET_MOUSE_BUTTON_ACTION
		call SerialTransmit_Host
		movf BUTTON_ACTION,W
		call SerialTransmit_Host
		movlw 5
		goto Send_Null_Bytes
Not_Mouse_Action
		movf Value,W
		sublw IKBD_STATUS_MOUSE_MODE_R
		btfsc STATUS,Z
			goto Mouse_Mode
		movf Value,W
		sublw IKBD_STATUS_MOUSE_MODE_A
		btfsc STATUS,Z
			goto Mouse_Mode
		movf Value,W
		sublw IKBD_STATUS_MOUSE_MODE_K
		btfss STATUS,Z
			goto Not_Mouse_Mode
Mouse_Mode
		movlw HEADER_STATUS; State Header
		call SerialTransmit_Host
		btfsc Flags2,MOUSE_KEYS
			goto Mouse_Mode_Keys
		btfsc Flags,MOUSE_ABS
			goto Mouse_Mode_Abs
		movlw IKBD_REL_MOUSE_POS_REPORT
		goto Send_End_Status_6_Null
Mouse_Mode_Abs
	 	movlw IKBD_ABS_MOUSE_POSITIONING
		call SerialTransmit_Host
		movf X_MAX_POSH,W; Absolute x position maximum mouse strong weight
		call SerialTransmit_Host; Xmsb, x maximum
		movf X_MAX_POSL,W; Absolute x position maximum mouse low weight
		call SerialTransmit_Host; Xlsb
		movf Y_MAX_POSH,W; Absolute position maximum mouse strong weight
		call SerialTransmit_Host; YMSB, Y Maximum
		movf Y_MAX_POSL,W; Absolute position maximum mice low weight
		call SerialTransmit_Host; Ylsb
		movlw 2
		goto Send_Null_Bytes		
Mouse_Mode_Keys
		movlw IKBD_SET_MOUSE_KEYCODE_CODE
		call SerialTransmit_Host
		movf DELTA_X,W; Deltax mode Keycode mouse ikbd
		call SerialTransmit_Host
		movf DELTA_Y,W; Deltay mode Keycode mouse ikbd
		goto Send_End_Status_4_Null
Not_Mouse_Mode
		movf Value,W
		sublw IKBD_STATUS_MOUSE_THRESHOLD
		btfss STATUS,Z
			goto Not_Threshold
		movlw HEADER_STATUS; State Header
		call SerialTransmit_Host
		movlw IKBD_SET_MOUSE_THRESHOLD
		call SerialTransmit_Host
		movlw 1
		call SerialTransmit_Host
		movlw 1
		goto Send_End_Status_4_Null
Not_Threshold
		movf Value,W
		sublw IKBD_STATUS_MOUSE_SCALE
		btfss STATUS,Z
			goto Not_Scale
		movlw HEADER_STATUS; State Header
		call SerialTransmit_Host
		movlw IKBD_SET_MOUSE_SCALE
		call SerialTransmit_Host
		movf X_SCALE,W
		call SerialTransmit_Host
		movf Y_SCALE,W
Send_End_Status_4_Null
		call SerialTransmit_Host
		movlw 4
		goto Send_Null_Bytes
Not_Scale
		movf Value,W
		sublw IKBD_STATUS_MOUSE_Y0_AT_B
		btfsc STATUS,Z
			goto Mouse_Vert
		movf Value,W
		sublw IKBD_STATUS_MOUSE_Y0_AT_T
		btfss STATUS,Z
			goto Not_Mouse_Vert
Mouse_Vert
		movlw HEADER_STATUS; State Header
		call SerialTransmit_Host
		movlw IKBD_SET_Y0_AT_BOTTOM
		btfss Flags,SIGN_Y
			movlw IKBD_SET_Y0_AT_TOP
		goto Send_End_Status_6_Null
Not_Mouse_Vert
		movf Value,W
		sublw IKDB_STATUS_DISABLE_MOUSE
		btfss STATUS,Z
			goto Not_Mouse_Enable
		movlw HEADER_STATUS; State Header
		call SerialTransmit_Host
		clrw; Enabled
		btfss Flags,MOUSE_ENABLE
			movlw IKDB_DISABLE_MOUSE
		goto Send_End_Status_6_Null
Not_Mouse_Enable
		movf Value,W
		sublw IKBD_STATUS_JOY_MODE_E
		btfsc STATUS,Z
			goto Joy_Mode
		movf Value,W
		sublw IKBD_STATUS_JOY_MODE_I
		btfsc STATUS,Z
			goto Joy_Mode
		movf Value,W
		sublw IKBD_STATUS_JOY_MODE_K
		btfss STATUS,Z
			goto Not_Joy_Mode
Joy_Mode	
		movlw HEADER_STATUS; State Header
		call SerialTransmit_Host
		btfsc Flags2,JOY_KEYS
			goto Joy_Mode_Keys
		movlw IKBD_SET_JOY_EVNT_REPORT
		btfss Flags2,JOY_EVENT
			movlw IKBD_SET_JOY_INTERROG_MODE
		goto Send_End_Status_6_Null		
Joy_Mode_Keys	
		movlw IKBD_SET_JOY_KEYCODE_MODE
		call SerialTransmit_Host
		movf RX_JOY,W
		call SerialTransmit_Host; Rx
		movf RY_JOY,W
		call SerialTransmit_Host; Ry
		movf TX_JOY,W
		call SerialTransmit_Host; Tx
		movf TY_JOY,W
		call SerialTransmit_Host; Ty
		movf VX_JOY,W
		call SerialTransmit_Host; Vx
		movf VY_JOY,W
		call SerialTransmit_Host; Vy
		goto Main
Not_Joy_Mode
		movf Value,W
		sublw IKDB_STATUS_DISABLE_JOY
		btfss STATUS,Z
			goto Main
		movlw HEADER_STATUS; State Header
		call SerialTransmit_Host
		clrw; Enabled
		btfss Flags,JOY_ENABLE
			movlw IKDB_DISABLE_JOYSTICKS
Send_End_Status_6_Null
		call SerialTransmit_Host
		movlw 6
Send_Null_Bytes
		call TransmitNullBytes; end status
		goto Main

; -----------------------------------------------------------------
; Keyboard errors
; -----------------------------------------------------------------

Error_Keyboard
		call Remove_Key_Forced
		call cmdResetKey
		goto Main

Error_Parity_Keyboard
		call cmdResendKey
		goto Main

; -----------------------------------------------------------------
; Data from the keyboard
; -----------------------------------------------------------------

doKeyboard
		; Prohibit all emissions from peripherals PS/2 (Mouse and Keyboard)
		DISABLEKEYB
		btfss PARITY,7
			goto Error_Parity_Keyboard; Break error
		; Is this the byte of the Bat Tipboard order?
		movf Value,W
		sublw CMD_BAT; Self-test passed (Keyboard Controller Init)
		btfsc STATUS,Z; Wuts $ aa?
			goto OnKbBAT
		movf Value,W
		sublw BAT_ERROR; Keyboard error
		btfsc STATUS,Z
			goto Error_Keyboard
		movf Value,W
		sublw ACK_ERROR; Keyboard error
		btfsc STATUS,Z
			goto Error_Keyboard

		; No, other byte, we continue according to the mode
		; PS/2 Direct or Atari Tranlation

		IF SERIAL_DEBUG
		btfsc PORTB,JUMPER4; If Jumper4 (+5V): Atari mode
			goto ModeKeyAtari
; -----------------------------------------------------------------
; PC mode: no translation, direct sending of scan-codes in text
; ASCII (BCD) or binaries directly

		bcf PORTB,LEDGREEN; LED keyboard lighter
		movf Value,W; keyboard code
		call SerialTransmit_Host
		bsf PORTB,LEDGREEN; Eteint LED Keyboard
		goto Main
		ENDIF
		
; -----------------------------------------------------------------
; Atari mode: PC translate -> Atari Scancodes

ModeKeyAtari
		btfss Flags3,KEYB_SET_2
			goto Set3
		btfsc Flags3,PAUSE_SET_2
			goto TraiterPause
		movf Value,W
		sublw ESCAPE                    ; does w contain $ e0?
		btfss STATUS,Z                  ; Yes, pass
			goto TestPauseSet2          ; SPECIAL CASE PAUSE 2
		bsf Flags3,NEXT_CODE            ; Next Code Process
		IF LCD
		IF !LCD_DEBUG
		btfss Flags4,LCD_ENABLE         ; LCD Enabled?
			goto Main
		movlw 0x8E                      ; line 1, column 15
		bsf PCLATH,3                    ; Page 1 gold 3 (0x800 - 0xfff)
		call Send_Value_Lcd
		bcf PCLATH,3                    ; page 0 2
		ENDIF
		ENDIF
                goto Main
TestPauseSet2
		movf Value,W
		sublw ESCAPE1                   ; does w contain $ e1?
		btfss STATUS,Z                  ; Yes, pass
			goto Set3
		bsf Flags3,NEXT_CODES           ; Next Codes Process
		bsf Flags3,PAUSE_SET_2
		goto Main
TraiterPause
		btfsc Flags3,NEXT_CODES
			goto TraiterPause2
		movf Value,W
		sublw CMD_RELEASED              ; Dues w contain $ f0?
		btfsc STATUS,Z                  ; Yes, pass
			goto BreakCode
		bcf Flags3,NEXT_CODES
		bcf Flags2,BREAK_CODE           ; Key Pressed by Default
		bsf Flags3,NEXT_CODE            ; Next Code Process
                goto Main
TraiterPause2
		movf Value,W
		sublw CMD_RELEASED              ; Dues w contain $ f0?
		btfsc STATUS,Z                  ; Yes, pass
			goto BreakCode
		movf Value,W
		sublw 0x77                      ; does w contain $ 77?
        btfss STATUS,Z                  ; Yes, pass
               	goto Not_SendKey
		btfsc Flags2,JOY_MONITOR
			goto Not_SendPause
		bcf PORTB,LEDGREEN              ; Keyboard led on
            	movlw DEF_PAUSE         ; Key Pressed
		btfsc Flags2,BREAK_CODE
            iorlw 0x80                  ; Released (Breakcode bit7 = 1)
		call SerialTransmit_Host
		bsf PORTB,LEDGREEN              ; Keyb LED OFF
Not_SendPause
		bcf Flags3,PAUSE_SET_2
		goto Not_SendKey
Set3
		movf Value,W
		sublw CMD_RELEASED              ; Dues w contain $ f0?
		btfss STATUS,Z                  ; Yes, pass
			goto Not_BreakCode
BreakCode
		bsf Flags2,BREAK_CODE           ; Process Break Code (Key Release)
            goto Main
Not_BreakCode
		btfsc Flags2,JOY_MONITOR
			goto Not_SendKey
		IF LCD
		IF !LCD_DEBUG
		btfss Flags4,LCD_ENABLE         ; LCD Enabled?
			goto ByPass_Lcd
		movlw 0xCE                      ; line 2, column 15
		bsf PCLATH,3                    ; Page 1 gold 3 (0x800 - 0xfff)
		call Send_Value_Lcd
		bcf PCLATH,3                    ; page 0 2
ByPass_Lcd
		ENDIF
		ENDIF
		bcf PORTB,LEDGREEN              ; Keyboard led on
		call SendAtariKeyboard
		bsf PORTB,LEDGREEN              ; Keyb LED OFF
Not_SendKey
		bcf Flags2,BREAK_CODE           ; Key Pressed by Default
		bcf Flags3,NEXT_CODE            ; FLAG 2nd Code after 0X0
		goto Main

; -----------------------------------------------------------------
; Receive beats Keyboard Command
; -----------------------------------------------------------------

OnKbBAT
		call KbBAT
		bsf Status_Boot,POWERUP_KEYB
		goto Main

KbBAT
; After Reset.
; Delay: 500 ms, spleen; 10.9 CPS, set 2, Typematic/Make/Break
		call cmdScanSet
		btfss Flags3,KEYB_SET_2
			call cmdMakeBreak
; BTFSC flags3, keyb_set_2
; Call cmdtyperate
		movlw CAPS_OFF      ; Enable Num-Lock, Disable Caps-Lock
		call cmdLedOnOff
		call cmdEnableKey
		bsf PORTB,LEDGREEN  ; Disable green led to show onbat
		return

; -----------------------------------------------------------------
; Mouse Errors
; -----------------------------------------------------------------

Error_Mouse
		call cmdResetMouse
		goto Main
		
Error_Parity_Mouse
		IF SCROOL_LOCK_ERR
		call UpdateLedOnOff
		ENDIF
		call cmdResendMouse
		clrf Counter_Mouse; Resend Whole Frame
		goto Main

; -----------------------------------------------------------------
; Date arrived from the mouse
; -----------------------------------------------------------------
		
doMouse
		; Prohibit all emissions from peripherals PS/2 (Mouse and Keyboard)
		DISABLEMOUSE
		btfss PARITY,7
			goto Error_Parity_Mouse
		movf Counter_Mouse,W
		btfss STATUS,Z
			goto Not_BatMouse; <> 1st byte
		; Is this the byte of the Bat Souris command?
		movf Value,W
		sublw CMD_BAT; Self-test passed
		btfsc STATUS,Z; Wuts $ aa?
			goto OnMsBAT
		movf Value,W
		sublw BAT_ERROR; Mouse error
		btfsc STATUS,Z
			goto Error_Mouse
		movf Value,W
		sublw ACK_ERROR; Mouse error
		btfsc STATUS,Z
			goto Error_Mouse
Not_BatMouse
		IF SERIAL_DEBUG
		btfsc PORTB,JUMPER4; If Jumper4 (+5V): Atari mode
			goto ModeMsAtari
; -----------------------------------------------------------------
; PC mouse mode: Directly sends codes in ASCII (BCD) text codes or
; binary

		bcf PORTB,LEDYELLOW; Led mouse lighter
		movf Value,W
		call SerialTransmit_Host
		bsf PORTB,LEDYELLOW; Eteint Led mouse
		goto Main
		ENDIF

; -----------------------------------------------------------------
; Atari mouse mode: we convert the byte packets into a Atari frame

ModeMsAtari
		incf Counter_Mouse,F; counter to treat each byte received via the main loop (hand)
		movf Counter_Mouse,W
		sublw 1
		btfsc STATUS,Z
			goto First_Byte; 1st byte
		movf Counter_Mouse,W
		sublw 2
		btfsc STATUS,Z
			goto Second_Byte; 2nd byte (x)
		movf Counter_Mouse,W
		sublw 3
		btfsc STATUS,Z
			goto Third_Byte; 3rd byte (y)
		goto Fourth_Byte; 4th Event byte (Z)
First_Byte		
		movf Value,W
		movwf Value_0; Value Value_0 test
		btfsc Value_0,7
			goto Pb_Trame_Mouse; Y Overflow
		btfsc Value_0,6
			goto Pb_Trame_Mouse; X overflow
		btfsc Value_0,3
			goto Main
		; bit 3 must always be 1
Pb_Trame_Mouse
		clrf Counter_Mouse; Drag in reading the frame
		goto Main
Second_Byte
		movf Value,W
		movwf Value_X; Value x Movement
		goto Main
Third_Byte		
		movf Value,W
		movwf Value_Y; Value Y Movement
		btfss Flags,MSWHEEL
			goto Normal_Mouse
		clrf Value_Z
		goto Main
Fourth_Byte
		movf Value,W
		movwf Value_Z; Value Z Mouvement (-8 to 7)
Normal_Mouse
		clrf Counter_Mouse
		clrf BUTTONS; mouse buttons
		btfsc Value_0,PC_LEFT; Test if left button smile at 1
			bsf BUTTONS,AT_LEFT; If 1 put the one atri to 1
		btfsc Value_0,PC_RIGHT; Test if right mouse at 1
			bsf BUTTONS,AT_RIGHT; If 1 Put the one at 1
		movf BUTTONS,W
		iorlw HEADER_RELATIVE_MOUSE; Header mouse relative mode (0xf8 - 0xfb)
		movwf HEADER_IKBD		

		; ----------------------------------------------------------------------------
		; Instead of simulating right and left support, we generate a scan-code
                ; we write 0 so as not to transmit then
		clrf CLIC_MOUSE_WHEEL; button 3 key
		clrf KEY_MOUSE_WHEEL; button roulette key 3
		clrf KEY2_MOUSE_WHEEL; 4 & 5 button button
		btfss Value_0,PC_MIDDLE; Test if central button mouse at 1
			goto Compteurs_Mouse
		movlw Tab_Mouse-EEProm+IDX_BUTTON3
		call Lecture_EEProm
		movwf CLIC_MOUSE_WHEEL
		; ----------------------------------------------------------------------------
Compteurs_Mouse
		; ----------------------------------------------------------------------------
		; Treat the X counter
		bcf Value_X,AT_SIGN; Bring the value back to 7 bits
		btfsc Value_0,PC_SIGNX; Test the PC sign bit for x
			bsf Value_X,AT_SIGN; is raised so we raise the Atari sign
		movf Value_X,W
		movwf X_MOV; Write the result in the X Atari counter
		btfss Flags,MOUSE_ABS
			goto Not_Max_X; <> Absolute fashion
		clrf TEMP2; positive
		btfsc Value_X,7
			comf TEMP2,F; negative
		addwf X_POSL,F; ABSOLUE SOUS POSEMENT SOUS Low weight
		movf TEMP2,W
		btfsc STATUS,C
			incfsz TEMP2,W
		addwf X_POSH,F; X_pos = x_pos + x_mov
		btfsc X_POSH,7; Absolute mouse position x
			goto Dep_Min_X; If x_pos <0 -> x_pos = 0
		bsf PCLATH,3; Page 1 or 3 (0x800 - 0xfff)
		call Conv_Scale_X
		bcf PCLATH,3; page 0 or 2
		movf X_MAX_POSH,W; Absolute x position maximum mouse strong weight
		subwf X_POSH_SCALED,W; absolute mouse x position with strong weight factor
		btfsc STATUS,Z
			goto XCompl
		btfss STATUS,C
			goto Not_Max_X; X_pos <x_max_pos
		goto Dep_Max_X; X_pos> x_max_pos
XCompl		movf X_MAX_POSL,W; Absolute x position maximum mouse low weight
		subwf X_POSL_SCALED,W; absolute mouse x position with low weight factor factor
		btfsc STATUS,Z
			goto Dep_Max_X; X_pos = x_max_pos
		btfss STATUS,C
			goto Not_Max_X; X_pos <x_max_pos
Dep_Max_X
		movf X_MAX_POSL,W
		movwf X_POSL_SCALED
		movf X_MAX_POSH,W
		movwf X_POSH_SCALED; If x_pos> = x_max_pos -> x_pos = x_max_pos
		bsf PCLATH,3; Page 1 or 3 (0x800 - 0xfff)
		call Conv_Inv_Scale_X
		bcf PCLATH,3; page 0 or 2
		goto Not_Max_X
Dep_Min_X
		call Init_X_Abs
Not_Max_X
		; ----------------------------------------------------------------------------
		; Treat the meter y
		bcf Value_Y,AT_SIGN; Bring the value back to 7 bits
		btfsc Value_0,PC_SIGNY; Test the PC sign bit for y
			bsf Value_Y,AT_SIGN; is raised so we raise the Atari sign
                ; The PS/2 movement and Atari is opposite by default
		btfsc Flags,SIGN_Y
			goto Not_Inv_Y; Reversion of meaning y ikbd
		; Completely has two to reverse the Y movement: we only treat +127/-128
		; Ex: $ ff %11111111 D-1 => $ 01 %00000001 D+1
		comf Value_Y,F
		incf Value_Y,F
Not_Inv_Y
		movf Value_Y,W
		movwf Y_MOV; Write the result in the Y -Etari counter
		btfss Flags,MOUSE_ABS
			goto Not_Max_Y; <> Absolute fashion
		clrf TEMP2; positive
		btfsc Value_Y,7
			comf TEMP2,F; negative
		addwf Y_POSL,F; ABSOLUE MOUSE POST MOUSE Low weight
		movf TEMP2,W
		btfsc STATUS,C
			incfsz TEMP2,W
		addwf Y_POSH,F; Y_pos = y_pos + y_mov
		btfsc Y_POSH,7; Absolute mouse position
			goto Dep_Min_Y; If y_pos <0 -> y_pos = 0
		bsf PCLATH,3; Page 1 or 3 (0x800 - 0xfff)
		call Conv_Scale_Y
		bcf PCLATH,3; page 0 or 2
		movf Y_MAX_POSH,W; Absolute position maximum mouse strong weight
		subwf Y_POSH_SCALED,W; ABSOLUE MOUSE POSEMENT WITH FORCE FORTOR
		btfsc STATUS,Z
			goto YCompl
		btfss STATUS,C
			goto Not_Max_Y; Y_pos <y_max_pos
		goto Dep_Max_Y; Y_pos> y_max_pos
YCompl
		movf Y_MAX_POSL,W; Absolute position maximum mice low weight
		subwf Y_POSL_SCALED,W; Absolute mouse position with low weight factor factor
		btfsc STATUS,Z
			goto Dep_Max_Y; X_pos = y_max_pos
		btfss STATUS,C
			goto Not_Max_Y; Y_pos <y_max_pos
Dep_Max_Y
		movf Y_MAX_POSL,W
		movwf Y_POSL_SCALED
		movf Y_MAX_POSH,W
		movwf Y_POSH_SCALED; If y_pos> = y_max_pos -> y_pos = y_max_pos
		bsf PCLATH,3; Page 1 or 3 (0x800 - 0xfff)
		call Conv_Inv_Scale_Y
		bcf PCLATH,3; page 0 or 2
		goto Not_Max_Y
Dep_Min_Y
		call Init_Y_Abs
Not_Max_Y
		; -------------------------------------------------------------------------------------------------------
		; We receive the Z counter, if it's a roulette mouse
		btfss Flags,MSWHEEL
			goto TransmitHost; If bit mouse with roulette in zero we now transmit
		; Case of the Intelimouse, treat the Z counter
		btfsc Value_Z,PC_SIGNZ; Is this a negative value
			goto ZNegatif
		; Testing whether the value on the 4bits [3-0] is equal to 0 or not
		movf Value_Z,W; Load w with the value
		andlw 0x0F; Hide and treat the Z counter on 4 bits
		btfsc STATUS,Z
			goto ZZero
		; ----------------------------------------------------------------------------
		; Positive value: vertical wheel downwards
		; or horizontal wheel to the right
		btfss Value_Z,PC_BITLSBZ; If the bit 0 is 1 we therefore 0x1 => vertical wheel
			goto ZGauche; go to a horizontal wheel
		movlw Tab_Mouse-EEProm+IDX_WHEELDN
		call Lecture_EEProm
		movwf KEY_MOUSE_WHEEL; positive value therefore at the bottom any
		goto ZZero
ZGauche
		movlw Tab_Mouse-EEProm+IDX_WHEELLT
		call Lecture_EEProm
		movwf KEY_MOUSE_WHEEL; positive value therefore on the left all
		goto ZZero
ZNegatif
		; ----------------------------------------------------------------------------
		; Negative value: vertical wheel upwards
		; or horizontal wheel to the left
		btfss Value_Z,PC_BITLSBZ; If the bit 0 is 1 we therefore 0xf => vertical wheel
			goto ZDroit; go to a horizontal wheel
		movlw Tab_Mouse-EEProm+IDX_WHEELUP
		call Lecture_EEProm
		movwf KEY_MOUSE_WHEEL; Negative value -1 therefore above all
		goto ZZero
ZDroit
		movlw Tab_Mouse-EEProm+IDX_WHEELRT
		call Lecture_EEProm
		movwf KEY_MOUSE_WHEEL; Negative value -2 So on the right all
ZZero
		; ----------------------------------------------------------------------------
		; If the intelimouse and 5 buttons test the state
		btfss Flags,MSWHEELPLUS; If bit Wheelplus to Zero we transmit now, he has no
			goto TransmitHost; buttons 4 & 5 and 2nd dial
		btfss Value_Z,PC_BUTTON4; Active 4 button?
			goto Prochain_Bouton; Test the next button (5)
		movlw Tab_Mouse-EEProm+IDX_BUTTON4
		call Lecture_EEProm
		movwf KEY2_MOUSE_WHEEL; Scan-Code combines button 4
		goto TransmitHost; We transmit now
Prochain_Bouton
		btfss Value_Z,PC_BUTTON5; ; Active 5 button?
			goto TransmitHost; We transmit now
		movlw Tab_Mouse-EEProm+IDX_BUTTON5
		call Lecture_EEProm
		movwf KEY2_MOUSE_WHEEL; Scan-Code combines button 5
TransmitHost
		; ----------------------------------------------------------------------------
		; Finally send the mouse package to host
		btfss Flags,MOUSE_ENABLE
			goto Main; No authorization from Atari
		btfsc Flags2,JOY_MONITOR
			goto Main; Monitoring Joysticks in progress requests by Atari
		bcf PORTB,LEDYELLOW; Led mouse lighter
		call SendAtariMouse; relative
		; ----------------------------------------------------------------------------
		; IKBD Button Action mode test
		btfss BUTTON_ACTION,0; Struck button => sending absolute position
			goto Not_Action_0
		movf BUTTONS,W; mouse buttons
		xorwf OLD_BUTTONS,W; Former state of mouse buttons
		andlw 1		
		btfsc STATUS,Z
			goto Not_Change_A
		btfsc BUTTONS,0
			goto Env_Action; right button
Not_Change_A
		movf BUTTONS,W; mouse buttons
		xorwf OLD_BUTTONS,W; Former state of mouse buttons
		andlw 2		
		btfsc STATUS,Z
			goto Not_Action_0
		btfsc BUTTONS,1
			goto Env_Action; Left button drives
Not_Action_0
		btfss BUTTON_ACTION,1; Refshor button => sending absolute position
			goto Not_Action_1	
		movf BUTTONS,W; mouse buttons
		xorwf OLD_BUTTONS,W; Former state of mouse buttons
		andlw 1		
		btfsc STATUS,Z
			goto Not_Change_B
		btfss BUTTONS,0
			goto Env_Action; Right drop -down button
Not_Change_B
		movf BUTTONS,W; mouse buttons
		xorwf OLD_BUTTONS,W; Former state of mouse buttons
		andlw 2		
		btfsc STATUS,Z
			goto Not_Action_1
		btfsc BUTTONS,1; Left button releases
			goto Not_Action_1
Env_Action
		movf BUTTONS,W; mouse buttons
		movwf OLD_BUTTONS_ABS; Old state of mouse buttons in absolute mode
		comf OLD_BUTTONS_ABS,F; force the sending of state changes
		movlw HEADER_ABSOLUTE_MOUSE; Header mouse absolute fashion
		movwf HEADER_IKBD
		call SendAtariMouse
Not_Action_1
		bsf PORTB,LEDYELLOW; Eteint Led mouse
		movf BUTTONS,W; mouse buttons
		movwf OLD_BUTTONS; Former state of mouse buttons
		goto Main

; -----------------------------------------------------------------
; Reception of the Bat Souris command
; -----------------------------------------------------------------

OnMsBAT
		call TryWheel; Detect if the mouse is with roulette
		btfsc Flags,MSWHEEL; If it's a roulette mouse
			call TryWheelPlus; Detect if is even more
		call cmdEnableMous
		bsf PORTB,LEDYELLOW; Turn off the yellow LED to show onbat
		bsf Status_Boot,POWERUP_MOUSE
		goto Main
		
; ====================================================================================================================================
; Procedures and functions
; ====================================================================================================================================

; -----------------------------------------------------------------
; Forcing 1 if 0
; -----------------------------------------------------------------
		
Change_0_To_1
		iorlw 0
		btfsc STATUS,Z
			movlw 1
		return
		
; -----------------------------------------------------------------
; Discount to 0 variables
; -----------------------------------------------------------------
		
Init_X_Y_Abs
		call Init_X_Abs

Init_Y_Abs
		clrf Y_POSL
		clrf Y_POSH
		clrf Y_POSL_SCALED; Absolute mouse position with low weight factor factor
		clrf Y_POSH_SCALED; ABSOLUE MOUSE POSEMENT WITH FORCE FORTOR
		return
		
Init_X_Abs	
		clrf X_POSL
		clrf X_POSH
		clrf X_POSL_SCALED; absolute mouse x position with low weight factor factor
		clrf X_POSH_SCALED; absolute mouse x position with strong weight factor
		return

; -----------------------------------------------------------------
; Byte transmission procedure About the clock
; -----------------------------------------------------------------
		
SendAtariClock
		movlw HEADER_TIME_OF_DAY; Header Clock
		call SerialTransmit_Host
		movlw LOW YEAR_BCD
		movwf FSR; point on the 1st element sent that is to say the year
		movlw 6; 6 bytes
		movwf Counter
Loop_Env_Time
			bsf STATUS,IRP; Page 2
			movf INDF,W
			call SerialTransmit_Host; YY, MM, DD, HH, MM, SS
			incf FSR,F
			decfsz Counter,F
		goto Loop_Env_Time; following element
		return

; -----------------------------------------------------------------
; Byte transmission procedure About (or) joystick (s)
; -----------------------------------------------------------------
		
SendAtariJoysticks
; -----------------------------------------------------------------
; Begin Fake Mouse Data (Right Mouse Button)-Added by MQ (2023-10-07)
		btfss Flags,MOUSE_ENABLE
			goto Not_Fake_Mouse_Data; No authorization from Atari
		movlw 0xF9; Joy1 Fire Pressed
		btfss JOY1,4
			movlw 0xF8; Joy1 Fire Released
		call SerialTransmit_Host
		movlw 0
		call SerialTransmit_Host
		movlw 0
		call SerialTransmit_Host
Not_Fake_Mouse_Data
; End Fake Mouse Data
; -----------------------------------------------------------------

		movf HEADER_IKBD,W
		sublw HEADER_JOYSTICKS; Header Joysticks
		btfss STATUS,Z
			goto Not_Joy01
		; ----------------------------------------------------------------------------
		; Transmit the Atari package (3 bytes) of the joysticks
		movf HEADER_IKBD,W
		call SerialTransmit_Host
	 	movf JOY0,W; Joystick 0 reading 0
		call SerialTransmit_Host_Joy
	 	movf JOY1,W; Reading Joystick 1
		goto SerialTransmit_Host_Joy
Not_Joy01
		movf HEADER_IKBD,W
		sublw HEADER_JOYSTICK0; Header Joystick 0
		btfss STATUS,Z
			goto Not_Joy0
		btfss Flags2,JOY_KEYS; Shipping items
			goto Not_ButAct0
		; ----------------------------------------------------------------------------
		; Transmit Button Action Joystick 0
		movlw 0x74; Joystick button 0 drives
		btfss JOY0,4
			movlw 0xF4; JYYSTICK button 0 RAPCH
		goto SerialTransmit_Host
Not_ButAct0
		; ----------------------------------------------------------------------------
		; Transmit the standard Atari (2 bytes) package of the JYYSTICK 0
		movf HEADER_IKBD,W
		call SerialTransmit_Host
		movf JOY0,W; Joystick 0 reading 0
		goto SerialTransmit_Host_Joy
Not_Joy0
		btfss Flags2,JOY_KEYS; Shipping items
			goto Not_ButAct1
		; ----------------------------------------------------------------------------
		; Transmit Button Action Joystick 1
		movlw 0x75; Joystick button 1 Punish
		btfss JOY1,4
			movlw 0xF5; Joystick button 1 release
		goto SerialTransmit_Host
Not_ButAct1
		; ----------------------------------------------------------------------------
		; Transmit the standard Atari (2 bytes) package of the joystick 1
		movf HEADER_IKBD,W
		call SerialTransmit_Host
		movf JOY1,W; Reading Joystick 1
SerialTransmit_Host_Joy
		; DEPLACTION OF THE JOYSTICK BIT FIRE (4 -> 7)
		movwf TEMP1
		btfsc TEMP1,4
			bsf TEMP1,7; Fire button
		bcf TEMP1,4
		movf TEMP1,W
		goto SerialTransmit_Host
		
; -----------------------------------------------------------------
; Bytes transmission procedure About Emulation
; Keyboard arrows via the joystick 0, ie the IKBD mode
; Keycodes joystick
; - Initial time RX/RY Decleche when supporting the direction
; scan-code of the keyboard is then sent a 1st time following
; The direction chosen on the JYYSTICK 0
; - Repetition time tx/ty (x times next vx/vy)
; - Total time VX/VY causing the stop of sending the scan-code of the
; keyboard arrow (ditto if relating to the chosen direction of the
; JOYSTICK 0)
; -----------------------------------------------------------------

SendAtariJoysticks_Fleches
		btfsc Status_Joy,RY_H
			goto Not_H
		movf JOYB,W; JYYSTICK 0
		xorwf OLD_JOY,W
		andlw 1		
		btfsc STATUS,Z
			goto Not_H; No change of state
		btfss JOYB,0
			goto Not_H
		bsf Status_Joy,RY_H; high button
		bcf Status_Joy,TY_H
		movf Counter_100MS_Joy,W
		movwf START_RY_JOY
		movf RY_JOY,W
		btfsc STATUS,Z
			goto Not_H; Ry time
		call SerialTransmit_Haut; 1st sending
Not_H
		btfsc Status_Joy,RY_B
			goto Not_B
		movf JOYB,W
		xorwf OLD_JOY,W
		andlw 2		
		btfsc STATUS,Z
			goto Not_B; No change of state
		btfss JOYB,1
			goto Not_B
		bsf Status_Joy,RY_B; Bas button drives
		bcf Status_Joy,TY_B
		movf Counter_100MS_Joy,W
		movwf START_RY_JOY
		movf RY_JOY,W
		btfsc STATUS,Z
			goto Not_B; Ry time
		call SerialTransmit_Bas; 1st sending
Not_B
		btfsc Status_Joy,RX_G
			goto Not_G
		movf JOYB,W
		xorwf OLD_JOY,W
		andlw 4		
		btfsc STATUS,Z
			goto Not_G; No change of state
		btfss JOYB,2
			goto Not_G
		bsf Status_Joy,RX_G; Left button drives
		bcf Status_Joy,TX_G
		movf Counter_100MS_Joy,W
		movwf START_RX_JOY
		movf RX_JOY,W
		btfsc STATUS,Z
			goto Not_G; time rx
		call SerialTransmit_Gauche; 1st sending
Not_G
		btfsc Status_Joy,RX_D
			goto Not_D
		movf JOYB,W
		xorwf OLD_JOY,W
		andlw 8		
		btfsc STATUS,Z
			goto Not_D; No change of state
		btfss JOYB,3
			goto Not_D
		bsf Status_Joy,RX_D; right button
		bcf Status_Joy,TX_D
		movf Counter_100MS_Joy,W
		movwf START_RX_JOY
		movf RX_JOY,W
		btfsc STATUS,Z
			goto Not_D; time rx
		call SerialTransmit_Droite; 1st sending
Not_D
		btfss Status_Joy,RY_H
			goto Not_H2
		btfss JOYB,0
			goto End_H; High release button
		movf START_RY_JOY,W
		subwf Counter_100MS_Joy,W
		subwf VY_JOY,W; VY - Time Lécoule
		btfsc STATUS,C
			goto Not_H3
End_H
		bcf Status_Joy,RY_H; Total end
		bcf Status_Joy,TY_H
		goto Not_H2
Not_H3
		btfsc Status_Joy,TY_H
			goto Not_H4; Repetition time
		movf START_RY_JOY,W
		subwf Counter_100MS_Joy,W
		subwf RY_JOY,W; Ry - Time Ecoule
		btfsc STATUS,C
			goto Not_H2; <> End 1st time
		goto Delay_TY_H
Not_H4
		movf START_TY_JOY,W
		subwf Counter_100MS_Joy,W
		subwf TY_JOY,W; Ty - Time Live
		btfsc STATUS,C
			goto Not_H2
Delay_TY_H
		bsf Status_Joy,RY_H
		bsf Status_Joy,TY_H
		movf Counter_100MS_Joy,W
		movwf START_TY_JOY
		call SerialTransmit_Haut; repetition
Not_H2
		btfss Status_Joy,RY_B
			goto Not_B2
		btfss JOYB,1
			goto End_B; Low drop button
		movf START_RY_JOY,W
		subwf Counter_100MS_Joy,W
		subwf VY_JOY,W; VY - Time Lécoule
		btfsc STATUS,C
			goto Not_B3
End_B
		bcf Status_Joy,RY_B; Total end
		bcf Status_Joy,TY_B
		goto Not_B2
Not_B3
		btfsc Status_Joy,TY_B
			goto Not_B4; Repetition time
		movf START_RY_JOY,W
		subwf Counter_100MS_Joy,W
		subwf RY_JOY,W; Ry - Time Ecoule
		btfsc STATUS,C
			goto Not_B2; <> End 1st time
		goto Delay_TY_B
Not_B4
		movf START_TY_JOY,W
		subwf Counter_100MS_Joy,W
		subwf TY_JOY,W; Ty - Time Live
		btfsc STATUS,C
			goto Not_B2
Delay_TY_B
		bsf Status_Joy,RY_B
		bsf Status_Joy,TY_B
		movf Counter_100MS_Joy,W
		movwf START_TY_JOY
		call SerialTransmit_Bas; repetition
Not_B2
		btfss Status_Joy,RX_G
			goto Not_G2
		btfss JOYB,2
			goto End_G; Left button releases
		movf START_RX_JOY,W
		subwf Counter_100MS_Joy,W
		subwf VX_JOY,W; VX - ECOULE TIME
		btfsc STATUS,C
			goto Not_G3
End_G
		bcf Status_Joy,RX_G; Total end
		bcf Status_Joy,TX_G
		goto Not_G2
Not_G3
		btfsc Status_Joy,TX_G
			goto Not_G4; Repetition time
		movf START_RX_JOY,W
		subwf Counter_100MS_Joy,W
		subwf RX_JOY,W; RX - ECOULE TIME
		btfsc STATUS,C
			goto Not_G2; <> End 1st time
		goto Delay_TX_G
Not_G4
		movf START_TX_JOY,W
		subwf Counter_100MS_Joy,W
		subwf TX_JOY,W; TX - ECOULE TIME
		btfsc STATUS,C
			goto Not_G2
Delay_TX_G
		bsf Status_Joy,RX_G
		bsf Status_Joy,TX_G
		movf Counter_100MS_Joy,W
		movwf START_TX_JOY
		call SerialTransmit_Gauche; repetition
Not_G2
		btfss Status_Joy,RX_D
			goto Not_D2
		btfss JOYB,3
			goto End_D; Right drop -down button
		movf START_RX_JOY,W
		subwf Counter_100MS_Joy,W
		subwf VX_JOY,W; VX - ECOULE TIME
		btfsc STATUS,C
			goto Not_D3
End_D
		bcf Status_Joy,RX_D; Total end
		bcf Status_Joy,TX_D
		goto Not_D2
Not_D3
		btfsc Status_Joy,TX_D
			goto Not_D4; Repetition time
		movf START_RX_JOY,W
		subwf Counter_100MS_Joy,W
		subwf RX_JOY,W; RX - ECOULE TIME
		btfsc STATUS,C
			goto Not_D2; <> End 1st time
		goto Delay_TX_D
Not_D4
		movf START_TX_JOY,W
		subwf Counter_100MS_Joy,W
		subwf TX_JOY,W; TX - ECOULE TIME
		btfsc STATUS,C
			goto Not_D2
Delay_TX_D
		bsf Status_Joy,RX_D
		bsf Status_Joy,TX_D
		movf Counter_100MS_Joy,W
		movwf START_TX_JOY
		call SerialTransmit_Droite; repetition
Not_D2
		movf JOYB,W
		movwf OLD_JOY	
		return

; -----------------------------------------------------------------
; Bytes transmission procedure About the mouse. We send
; The standard Atari mouse package, out of 3 bytes and then if the bytes are no
; null, we send two supplements which contain scan-codes for
; The 4 & 5 plums and buttons.
; 
; ENTRES: HEADER, X_MOV, Y_MOV in IKBD MOUND
; Header, buttons, x_posh, x_posl, y_posh, y_posl absolutely
; Outings: w Destruit
; -----------------------------------------------------------------

SendAtariMouse
		movf HEADER_IKBD,W
		sublw HEADER_ABSOLUTE_MOUSE; Header mouse absolute fashion
		btfsc STATUS,Z
			goto SendAtariMouse_Abs; Absolute fashion
		btfsc Flags,MOUSE_ABS
			goto Not_trame_Rel; Mouse in absolute mode
		btfsc Flags2,MOUSE_KEYS; Shipping items
			goto Not_trame_Rel
		; ----------------------------------------------------------------------------
		; Transmit the standard Atari mouse package (3 bytes) Relative mode
		movf HEADER_IKBD,W
		call SerialTransmit_Host; Send the byte order to the host
		movf X_MOV,W; Relative DEPLACEMENT MOUSE IN X
		call SerialTransmit_Host; Send the counter X to the host
		movf Y_MOV,W; Deplacement Relative mouse in Y
		call SerialTransmit_Host; Send the byte counter y to the host
		; ----------------------------------------------------------------------------
Not_trame_Rel                      
		; ----------------------------------------------------------------------------
		; Ikbd Mouse Keycodes fashion test
		btfss Flags2,MOUSE_KEYS; Shipping items
			goto Not_Keys_Mouse
		movf X_MOV,W; Relative DEPLACEMENT MOUSE IN X
		addwf X_INC_KEY,F; Keycode mouse in x mode
		btfsc X_INC_KEY,7
			goto Loop_Moins_H
Loop_Plus_H
			movf DELTA_X,W; Deltax mode Keycode mouse ikbd
			subwf X_INC_KEY,W
			btfsc STATUS,C
				goto Not_Key_Mouse_H
			movwf X_INC_KEY
			call SerialTransmit_Droite
		goto Loop_Plus_H	
Loop_Moins_H
			movf DELTA_X,W; Deltax mode Keycode mouse ikbd
			addwf X_INC_KEY,W
			btfsc STATUS,C
				goto Not_Key_Mouse_H
			movwf X_INC_KEY
			call SerialTransmit_Gauche
		goto Loop_Moins_H	
Not_Key_Mouse_H
		movf Y_MOV,W; Deplacement Relative mouse in Y
		addwf Y_INC_KEY,F; Interect in Yeycode Mouse mode
		btfsc Y_INC_KEY,7
			goto Loop_Moins_V
Loop_Plus_V
			movf DELTA_Y,W; Deltay mode Keycode mouse ikbd
			subwf Y_INC_KEY,W
			btfsc STATUS,C
				goto Not_Keys_Mouse
			movwf Y_INC_KEY
			btfss Flags,SIGN_Y	
				call SerialTransmit_Bas
			btfsc Flags,SIGN_Y	
				call SerialTransmit_Haut
		goto Loop_Plus_V	
Loop_Moins_V
			movf DELTA_Y,W; Deltay mode Keycode mouse ikbd
			addwf Y_INC_KEY,W
			btfsc STATUS,C
				goto Not_Keys_Mouse
			movwf Y_INC_KEY
			btfss Flags,SIGN_Y	
				call SerialTransmit_Haut
			btfsc Flags,SIGN_Y	
				call SerialTransmit_Bas
		goto Loop_Moins_V
Not_Keys_Mouse
		; ----------------------------------------------------------------------------
		; IKBD Button Action mode test
		btfss BUTTON_ACTION,2; Sending buttons
			goto Not_Clic_Mouse
		movf BUTTONS,W; mouse buttons
		xorwf OLD_BUTTONS,W; Former state of mouse buttons
		andlw 1		
		btfsc STATUS,Z
			goto Not_Change_C
		movlw 0x75; right button
		btfss BUTTONS,0
			movlw 0xF5; Right drop -down button
		call SerialTransmit_Host
Not_Change_C
		movf BUTTONS,W; mouse buttons
		xorwf OLD_BUTTONS,W; Former state of mouse buttons
		andlw 2		
		btfsc STATUS,Z
			goto Not_Clic_Mouse
		movlw 0x74; Left button drives
		btfss BUTTONS,1
			movlw 0xF4; Left button releases
		call SerialTransmit_Host
Not_Clic_Mouse
		; ----------------------------------------------------------------------------
		; Transmit the scan code for the central button (if it is non-zero)
		movf CLIC_MOUSE_WHEEL,W; Test the evidence to transmit
		btfsc STATUS,Z
			goto Roulettes
		; Effective transmission: sending the scan-code for the central button
		call SerialTransmit_KeyUpDown; send the wheel
Roulettes
		; ----------------------------------------------------------------------------
		; Transmit the scan code of knobs (if it is not zero)
		movlw Tab_Mouse-EEProm+IDX_WHREPEAT
		call Lecture_EEProm; Number Repetitions Mouse Wheel Touche
		movwf Counter
Repeat
			movf KEY_MOUSE_WHEEL,W ; Test the evidence to transmit
			btfsc STATUS,Z
				goto Buttons45
			; Effective transmission: sending the scan-code for the wheel
			call SerialTransmit_KeyUpDown; send the wheel
			decfsz Counter,F; repeat the show
		goto Repeat
Buttons45
		; ----------------------------------------------------------------------------
		; Transmit the 4 & 5 buttons code (if it is non-zero)
		movf KEY2_MOUSE_WHEEL,W; ; Test the evidence to transmit
		btfsc STATUS,Z
			return
		goto SerialTransmit_KeyUpDown; Send the button 4 & 5
		; ----------------------------------------------------------------------------
SendAtariMouse_Abs
		; ----------------------------------------------------------------------------
		; Transmit the Atari mouse package (5 bytes) in absolute mode
		movf HEADER_IKBD,W
		call SerialTransmit_Host
		clrf TEMP1
		movf BUTTONS,W; mouse buttons
		; Right button change test test
		xorwf OLD_BUTTONS_ABS,W; Old state of mouse buttons in absolute mode
		andlw 1		
		btfsc STATUS,Z
			goto Not_Change_0
		btfsc BUTTONS,0
			bsf TEMP1,0; right button
		btfss BUTTONS,0
			bsf TEMP1,1; Right drop -down button
Not_Change_0
		; Test change of state of the left button
		movf BUTTONS,W; mouse buttons
		xorwf OLD_BUTTONS_ABS,W; Old state of mouse buttons in absolute mode
		andlw 2		
		btfsc STATUS,Z
			goto Not_Change_1
		btfsc BUTTONS,1
			bsf TEMP1,2; Left button drives
		btfss BUTTONS,1
			bsf TEMP1,3; Left button releases
Not_Change_1
		; Sending the Ikbd Mouse Mouse Fashion
		movf BUTTONS,W; mouse buttons
		movwf OLD_BUTTONS_ABS; Old state of mouse buttons in absolute mode
		movf TEMP1,W
		call SerialTransmit_Host; Buttercase changes: B3/2: Left releases/pushing, B1/0: Droit releases/Think
		movf X_POSH_SCALED,W; absolute mouse x position with strong weight factor
		call SerialTransmit_Host; Xsmb
		movf X_POSL_SCALED,W; absolute mouse x position with low weight factor factor
		call SerialTransmit_Host; Xlsb
		movf Y_POSH_SCALED,W; ABSOLUE MOUSE POSEMENT WITH FORCE FORTOR
		call SerialTransmit_Host; Ymsb
		movf Y_POSL_SCALED,W; Absolute mouse position with low weight factor factor
		goto SerialTransmit_Host; Ylsb
	
; -----------------------------------------------------------------
; Detection of a simple intelimouse mouse. We try the detection and we
; Position the MSWHEEL bit has such a roulette.
; 
; METHOD: Emit Sample Sample Rate 200
; Emit Sample Sample Rate 100
; Emit Sample Sample Rate 80
; 
; Emitting Get Device ID
; If returns 0x03 => mouse extended to roulette
; Otherwise return 0x00 => PS/2 Standard mouse
; -----------------------------------------------------------------

TryWheel
		; Send the parametering sequence to detect the type
		movlw 200
		call cmdSetSmpRate
		movlw 100
		call cmdSetSmpRate
		movlw 80
		call cmdSetSmpRate; Enter the Scrolling Wheel mode
		; Send the order for identification
		movlw GET_DEVICE_ID
		call MPSCmd
		; Wait now the mouse identification answer
		call MPSGet; Wait and Get Next byte
		; Analyze the return byte: 0x00 = PS/ 2 Standard/ 0x03 Intelimouse 3 buttons
		bcf Flags,MSWHEEL
		movf Value,W
		sublw MS_WHEEL; Subtract the Intelimouse code 3 buttons
		btfsc STATUS,Z
			bsf Flags,MSWHEEL; MS Scrolling Mouse
		; Just for Test: If BCD display Show the ID code of the mouse
		IF SERIAL_DEBUG
		movf Value,W
		btfss PORTB,JUMPER5; If Debug Mode
			call SerialTransmit_Host
		ENDIF
		movlw 100; Return the initial sampling rate
		goto cmdSetSmpRate; Leaving the mode
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
